MajenkoProjects/TerminalServer/TerminalServer/Firmware/src/config/default/driver/spi/src/drv_spi.c

/*******************************************************************************
  SPI Driver Implementation.

  Company:
    Microchip Technology Inc.

  File Name:
    drv_spi.c

  Summary:
    Source code for the SPI driver implementation.

  Description:
    This file contains the source code for the implementation of the SPI driver.
*******************************************************************************/

//DOM-IGNORE-BEGIN
/*******************************************************************************
* Copyright (C) 2018 Microchip Technology Inc. and its subsidiaries.
*
* Subject to your compliance with these terms, you may use Microchip software
* and any derivatives exclusively with Microchip products. It is your
* responsibility to comply with third party license terms applicable to your
* use of third party software (including open source software) that may
* accompany Microchip software.
*
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
* IN NO EVENT WILL MICROCHIP BE LIABLE FOR ANY INDIRECT, SPECIAL, PUNITIVE,
* INCIDENTAL OR CONSEQUENTIAL LOSS, DAMAGE, COST OR EXPENSE OF ANY KIND
* WHATSOEVER RELATED TO THE SOFTWARE, HOWEVER CAUSED, EVEN IF MICROCHIP HAS
* BEEN ADVISED OF THE POSSIBILITY OR THE DAMAGES ARE FORESEEABLE. TO THE
* FULLEST EXTENT ALLOWED BY LAW, MICROCHIP'S TOTAL LIABILITY ON ALL CLAIMS IN
* ANY WAY RELATED TO THIS SOFTWARE WILL NOT EXCEED THE AMOUNT OF FEES, IF ANY,
* THAT YOU HAVE PAID DIRECTLY TO MICROCHIP FOR THIS SOFTWARE.
*******************************************************************************/
//DOM-IGNORE-END

// *****************************************************************************
// *****************************************************************************
// Section: Included Files
// *****************************************************************************
// *****************************************************************************

#include <string.h>
#include "configuration.h"
#include "driver/spi/drv_spi.h"
#include "system/debug/sys_debug.h"

// *****************************************************************************
// *****************************************************************************
// Section: Global Data
// *****************************************************************************
// *****************************************************************************

/* This is the driver instance object array. */
static CACHE_ALIGN DRV_SPI_OBJ gDrvSPIObj[DRV_SPI_INSTANCES_NUMBER];

// *****************************************************************************
// *****************************************************************************
// Section: File scope functions
// *****************************************************************************
// *****************************************************************************

static void lDRV_SPI_TX_DMA_CallbackHandler(SYS_DMA_TRANSFER_EVENT event, uintptr_t context);
static void lDRV_SPI_RX_DMA_CallbackHandler(SYS_DMA_TRANSFER_EVENT event, uintptr_t context);

static inline uint32_t  lDRV_SPI_MAKE_HANDLE(uint16_t token, uint8_t drvIndex, uint8_t index)
{
    return (((uint32_t)token << 16) | ((uint32_t)drvIndex << 8) | index);
}

static inline uint16_t lDRV_SPI_UPDATE_TOKEN(uint16_t token)
{
    token++;

    if (token >= DRV_SPI_TOKEN_MAX)
    {
        token = 1;
    }

    return token;
}

static void lDRV_SPI_DisableInterrupts(DRV_SPI_OBJ* dObj)
{
    bool interruptStatus;
    const DRV_SPI_INTERRUPT_SOURCES* intInfo = dObj->interruptSources;
    const DRV_SPI_MULTI_INT_SRC* multiVector = &intInfo->intSources.multi;
    /* Disable DMA interrupt */
    if((dObj->txDMAChannel != SYS_DMA_CHANNEL_NONE) && (dObj->rxDMAChannel != SYS_DMA_CHANNEL_NONE))
    {
        if (intInfo->isSingleIntSrc == true)
        {
            dObj->dmaInterruptStatus = SYS_INT_SourceDisable((INT_SOURCE)intInfo->intSources.dmaInterrupt);
        }
        else
        {
            /* Disable DMA interrupt sources */
            interruptStatus = SYS_INT_Disable();

            dObj->dmaTxChannelIntStatus = SYS_INT_SourceDisable((INT_SOURCE)multiVector->dmaTxChannelInt);
            dObj->dmaRxChannelIntStatus = SYS_INT_SourceDisable((INT_SOURCE)multiVector->dmaRxChannelInt);

            SYS_INT_Restore(interruptStatus);
        }
    }
    else
    {
        /* Disable SPI interrupt */
        if (intInfo->isSingleIntSrc == true)
        {
            dObj->spiInterruptStatus = SYS_INT_SourceDisable((INT_SOURCE)intInfo->intSources.spiInterrupt);
        }
        else
        {
            interruptStatus = SYS_INT_Disable();
            if(multiVector->spiTxReadyInt != -1)
            {
                dObj->spiTxReadyIntStatus = SYS_INT_SourceDisable((INT_SOURCE)multiVector->spiTxReadyInt);
            }
            if(multiVector->spiTxCompleteInt != -1)
            {
                dObj->spiTxCompleteIntStatus = SYS_INT_SourceDisable((INT_SOURCE)multiVector->spiTxCompleteInt);
            }
            if(multiVector->spiRxInt != -1)
            {
                dObj->spiRxIntStatus = SYS_INT_SourceDisable((INT_SOURCE)multiVector->spiRxInt);
            }
            SYS_INT_Restore(interruptStatus);
        }
    }
}

static void lDRV_SPI_EnableInterrupts(DRV_SPI_OBJ* dObj)
{
    bool interruptStatus;
    const DRV_SPI_INTERRUPT_SOURCES* intInfo = dObj->interruptSources;
    const DRV_SPI_MULTI_INT_SRC* multiVector = &intInfo->intSources.multi;
    /* Enable DMA interrupt */
    if((dObj->txDMAChannel != SYS_DMA_CHANNEL_NONE) && (dObj->rxDMAChannel != SYS_DMA_CHANNEL_NONE))
    {
        if (intInfo->isSingleIntSrc == true)
        {
            SYS_INT_SourceRestore((INT_SOURCE)intInfo->intSources.dmaInterrupt, dObj->dmaInterruptStatus);
        }
        else
        {
            interruptStatus = SYS_INT_Disable();

            /* Enable DMA interrupt sources */
            SYS_INT_SourceRestore((INT_SOURCE)multiVector->dmaTxChannelInt, dObj->dmaTxChannelIntStatus);
            SYS_INT_SourceRestore((INT_SOURCE)multiVector->dmaRxChannelInt, dObj->dmaRxChannelIntStatus);

            SYS_INT_Restore(interruptStatus);
        }
    }
    else
    {
        /* Enable SPI interrupt */
        if (intInfo->isSingleIntSrc == true)
        {
            SYS_INT_SourceRestore((INT_SOURCE)intInfo->intSources.spiInterrupt, dObj->spiInterruptStatus);
        }
        else
        {
            interruptStatus = SYS_INT_Disable();
            if(multiVector->spiTxReadyInt != -1)
            {
                SYS_INT_SourceRestore((INT_SOURCE)multiVector->spiTxReadyInt, dObj->spiTxReadyIntStatus);
            }
            if(multiVector->spiTxCompleteInt != -1)
            {
                SYS_INT_SourceRestore((INT_SOURCE)multiVector->spiTxCompleteInt,dObj->spiTxCompleteIntStatus);
            }
            if(multiVector->spiRxInt != -1)
            {
                SYS_INT_SourceRestore((INT_SOURCE)multiVector->spiRxInt, dObj->spiRxIntStatus);
            }
            SYS_INT_Restore(interruptStatus);
        }
    }
}


static bool lDRV_SPI_ResourceLock(DRV_SPI_OBJ * dObj)
{
    /* We will allow buffers to be added in the interrupt context of the SPI
     * driver. But we must make sure that if we are inside interrupt, then we
     * should not modify mutexes. */
    if(dObj->interruptNestingCount == 0U)
    {
        /* Grab a mutex. This is okay because we are not in an interrupt context */
        if(OSAL_MUTEX_Lock(&(dObj->mutexTransferObjects), OSAL_WAIT_FOREVER) == OSAL_RESULT_FAIL)
        {
            return false;
        }
        /* We will disable interrupts so that the queue status does not get updated asynchronously */
        lDRV_SPI_DisableInterrupts(dObj);
    }

    return true;
}

static void lDRV_SPI_ResourceUnlock(DRV_SPI_OBJ * dObj)
{
    if(dObj->interruptNestingCount == 0U)
    {
        lDRV_SPI_EnableInterrupts(dObj);

        /* Release mutex */
        (void) OSAL_MUTEX_Unlock(&(dObj->mutexTransferObjects));
    }
}

static DRV_SPI_CLIENT_OBJ * lDRV_SPI_DriverHandleValidate(DRV_HANDLE handle)
{
    /* This function returns the pointer to the client object that is
       associated with this handle if the handle is valid. Returns NULL
       otherwise. */

    uint32_t drvInstance = 0;
    DRV_SPI_CLIENT_OBJ* clientObj = (DRV_SPI_CLIENT_OBJ*)NULL;

    if((handle != DRV_HANDLE_INVALID) && (handle != 0U))
    {
        /* Extract the drvInstance value from the handle */
        drvInstance = ((handle & DRV_SPI_INSTANCE_MASK) >> 8);

        if (drvInstance >= DRV_SPI_INSTANCES_NUMBER)
        {
            return (NULL);
        }

        if ((handle & DRV_SPI_INDEX_MASK) >= gDrvSPIObj[drvInstance].nClientsMax)
        {
            return (NULL);
        }

        /* Extract the client index and obtain the client object */
        clientObj = &((DRV_SPI_CLIENT_OBJ *)gDrvSPIObj[drvInstance].clientObjPool)[handle & DRV_SPI_INDEX_MASK];

        if ((clientObj->clientHandle != handle) || (clientObj->inUse == false))
        {
            return (NULL);
        }
    }

    return(clientObj);
}

static DRV_SPI_TRANSFER_OBJ* lDRV_SPI_FreeTransferObjGet(DRV_SPI_CLIENT_OBJ* clientObj)
{
    uint32_t i;
    uint32_t index;
    DRV_SPI_OBJ* dObj = (DRV_SPI_OBJ* )&gDrvSPIObj[clientObj->drvIndex];
    DRV_SPI_TRANSFER_OBJ* pTransferObj = (DRV_SPI_TRANSFER_OBJ*)dObj->transferObjPool;

    i = 0;
    index = dObj->transferObjLastUsedIndex;
    while(i < dObj->transferObjPoolSize)
    {
        if (index >= dObj->transferObjPoolSize)
        {
            index = 0;
        }
        if (pTransferObj[index].inUse == false)
        {
            pTransferObj[index].inUse = true;
            pTransferObj[index].next = NULL;

            /* Generate a unique buffer handle consisting of an incrementing
             * token counter, driver index and the buffer index.
             */
            pTransferObj[index].transferHandle = (DRV_SPI_TRANSFER_HANDLE)lDRV_SPI_MAKE_HANDLE(
                dObj->spiTokenCount, (uint8_t)clientObj->drvIndex, (uint8_t)index);

            /* Update the token for next time */
            dObj->spiTokenCount = lDRV_SPI_UPDATE_TOKEN(dObj->spiTokenCount);

            dObj->transferObjLastUsedIndex = index + 1U;

            return &pTransferObj[index];
        }
        i++;
        index++;
    }
    return NULL;
}
/* MISRA C-2023 Rule 11.3, 11.8 deviated below. Deviation record ID -
   H3_MISRAC_2023_R_11_3_DR_1 & H3_MISRAC_2023_R_11_8_DR_1*/

static bool lDRV_SPI_TransferObjAddToList(
    DRV_SPI_OBJ* dObj,
    DRV_SPI_TRANSFER_OBJ* transferObj
)
{
    DRV_SPI_TRANSFER_OBJ** pTransferObjList;
    bool isFirstTransferInList = false;

    pTransferObjList = (DRV_SPI_TRANSFER_OBJ**)&(dObj->transferObjList);

    // Is the buffer object list empty?
    if (*pTransferObjList == NULL)
    {
        *pTransferObjList = transferObj;
        isFirstTransferInList = true;
    }
    else
    {
        // List is not empty. Iterate to the end of the buffer object list.
        while (*pTransferObjList != NULL)
        {
            if ((*pTransferObjList)->next == NULL)
            {
                // End of the list reached, add the buffer here.
                (*pTransferObjList)->next = transferObj;
                break;
            }
            else
            {
                pTransferObjList = (DRV_SPI_TRANSFER_OBJ**)&((*pTransferObjList)->next);
            }
        }
    }

    return isFirstTransferInList;
}

static DRV_SPI_TRANSFER_OBJ* lDRV_SPI_TransferObjListGet( DRV_SPI_OBJ* dObj )
{
    DRV_SPI_TRANSFER_OBJ* pTransferObj = NULL;

    // Return the element at the head of the linked list
    pTransferObj = (DRV_SPI_TRANSFER_OBJ*)dObj->transferObjList;

    return pTransferObj;
}

static void lDRV_SPI_RemoveTransferObjFromList( DRV_SPI_OBJ* dObj )
{
    DRV_SPI_TRANSFER_OBJ** pTransferObjList;

    pTransferObjList = (DRV_SPI_TRANSFER_OBJ**)&(dObj->transferObjList);

    // Remove the element at the head of the linked list
    if (*pTransferObjList != NULL)
    {
        /* Save the buffer object to be removed. Set the next buffer object as
         * the new head of the linked list. Reset the removed buffer object. */

        DRV_SPI_TRANSFER_OBJ* temp = *pTransferObjList;
        *pTransferObjList = (*pTransferObjList)->next;
        temp->currentState = DRV_SPI_TRANSFER_OBJ_IS_FREE;
        temp->next = NULL;
        temp->inUse = false;
    }
}

static void lDRV_SPI_RemoveClientTransfersFromList(
    DRV_SPI_OBJ* dObj,
    DRV_SPI_CLIENT_OBJ* clientObj
)
{
    DRV_SPI_TRANSFER_OBJ** pTransferObjList;
    DRV_SPI_TRANSFER_OBJ* delTransferObj = NULL;

    pTransferObjList = (DRV_SPI_TRANSFER_OBJ**)&(dObj->transferObjList);

    while (*pTransferObjList != NULL)
    {
        // Do not remove the buffer object that is already in process
        if (((*pTransferObjList)->clientHandle == clientObj->clientHandle) &&
                ((*pTransferObjList)->currentState == DRV_SPI_TRANSFER_OBJ_IS_IN_QUEUE))
        {
            // Save the node to be deleted off the list
            delTransferObj = *pTransferObjList;

            // Update the current node to point to the deleted node's next
            *pTransferObjList = (DRV_SPI_TRANSFER_OBJ*)(*pTransferObjList)->next;

            // Reset the deleted node
            delTransferObj->currentState = DRV_SPI_TRANSFER_OBJ_IS_FREE;
            delTransferObj->event = DRV_SPI_TRANSFER_EVENT_COMPLETE;
            delTransferObj->next = NULL;
            delTransferObj->inUse = false;
        }
        else
        {
            // Move to the next node
            pTransferObjList = (DRV_SPI_TRANSFER_OBJ**)&((*pTransferObjList)->next);
        }
    }
}

/* MISRA C-2023 Rule 11.1 deviated:2 Deviation record ID -  H3_MISRAC_2023_R_11_1_DR_1 */

static void lDRV_SPI_StartDMATransfer(DRV_SPI_TRANSFER_OBJ* transferObj)
{
    DRV_SPI_CLIENT_OBJ* clientObj;
    DRV_SPI_OBJ* dObj;
    uint32_t size = 0;
    /* To avoid unused build error */
    (void) size;

    /* Get the client object that owns this buffer */
    clientObj = &((DRV_SPI_CLIENT_OBJ *)gDrvSPIObj[((transferObj->clientHandle & DRV_SPI_INSTANCE_MASK) >> 8)].clientObjPool)
    [transferObj->clientHandle & DRV_SPI_INDEX_MASK];

    dObj = (DRV_SPI_OBJ*)&gDrvSPIObj[clientObj->drvIndex];

    /* Initialize the dummy data buffer with 0xFF */
    (void)memset(dObj->dummyDataBuffer, 0xFF, sizeof(dObj->dummyDataBuffer));

    transferObj->nBytesTransferred = 0;

    transferObj->txPending = transferObj->txSize;
    transferObj->rxPending = transferObj->rxSize;

    /* Register callbacks for DMA */
    SYS_DMA_ChannelCallbackRegister(dObj->txDMAChannel, lDRV_SPI_TX_DMA_CallbackHandler, (uintptr_t)transferObj);
    SYS_DMA_ChannelCallbackRegister(dObj->rxDMAChannel, lDRV_SPI_RX_DMA_CallbackHandler, (uintptr_t)transferObj);

    SYS_DMA_AddressingModeSetup(dObj->rxDMAChannel, SYS_DMA_SOURCE_ADDRESSING_MODE_FIXED, SYS_DMA_DESTINATION_ADDRESSING_MODE_INCREMENTED);
    SYS_DMA_AddressingModeSetup(dObj->txDMAChannel, SYS_DMA_SOURCE_ADDRESSING_MODE_INCREMENTED, SYS_DMA_DESTINATION_ADDRESSING_MODE_FIXED);

    if(clientObj->setup.dataBits == DRV_SPI_DATA_BITS_8)
    {
        SYS_DMA_DataWidthSetup(dObj->rxDMAChannel, SYS_DMA_WIDTH_8_BIT);
        SYS_DMA_DataWidthSetup(dObj->txDMAChannel, SYS_DMA_WIDTH_8_BIT);
    }
    else if (clientObj->setup.dataBits <= DRV_SPI_DATA_BITS_16)
    {
        SYS_DMA_DataWidthSetup(dObj->rxDMAChannel, SYS_DMA_WIDTH_16_BIT);
        SYS_DMA_DataWidthSetup(dObj->txDMAChannel, SYS_DMA_WIDTH_16_BIT);
    }
    else
    {
        SYS_DMA_DataWidthSetup(dObj->rxDMAChannel, SYS_DMA_WIDTH_32_BIT);
        SYS_DMA_DataWidthSetup(dObj->txDMAChannel, SYS_DMA_WIDTH_32_BIT);
    }

    if ((transferObj->txPending > 0U) && (transferObj->rxPending > 0U))
    {
        /* Find the lower value among rxPending and txPending*/

        (transferObj->txPending >= transferObj->rxPending) ?
            (size = transferObj->rxPending) : (size = transferObj->txPending);

        /* Calculate the remaining tx/rx bytes and total bytes transferred */
        transferObj->rxPending -= size;
        transferObj->txPending -= size;
        transferObj->nBytesTransferred += size;

        /* Always set up the rx channel first */
        (void) SYS_DMA_ChannelTransfer(dObj->rxDMAChannel, dObj->rxAddress, transferObj->pReceiveData, size);
        (void) SYS_DMA_ChannelTransfer(dObj->txDMAChannel, transferObj->pTransmitData, dObj->txAddress, size);
    }
    else
    {
        if (transferObj->rxPending > 0U)
        {
            /* txPending is 0. Need to use the dummy data buffer for transmission.
             * Find out the max data that can be received, given the limited size of the dummy data buffer.
             */
            (transferObj->rxPending > sizeof(dObj->dummyDataBuffer)) ?
                (size = sizeof(dObj->dummyDataBuffer)): (size = transferObj->rxPending);

            /* Calculate the remaining rx bytes and total bytes transferred */
            transferObj->rxPending -= size;
            transferObj->nBytesTransferred += size;

            /* Always set up the rx channel first */
            (void) SYS_DMA_ChannelTransfer(dObj->rxDMAChannel, dObj->rxAddress, transferObj->pReceiveData, size);
            (void) SYS_DMA_ChannelTransfer(dObj->txDMAChannel, dObj->dummyDataBuffer, dObj->txAddress, size);

        }
        else
        {
            /* rxPending is 0. Need to use the dummy data buffer for reception.
             * Find out the max data that can be transmitted, given the limited size of the dummy data buffer.
             */
            (transferObj->txPending > sizeof(dObj->dummyDataBuffer)) ?
                (size = sizeof(dObj->dummyDataBuffer)): (size = transferObj->txPending);

            /* Calculate the remaining tx bytes and total bytes transferred */
            transferObj->txPending -= size;
            transferObj->nBytesTransferred += size;

            /* Always set up the rx channel first */
            (void) SYS_DMA_ChannelTransfer(dObj->rxDMAChannel, dObj->rxAddress, dObj->dummyDataBuffer, size);
            (void) SYS_DMA_ChannelTransfer(dObj->txDMAChannel, transferObj->pTransmitData, dObj->txAddress, size);
        }
    }
}
/* MISRAC 2012 deviation block end */

static void lDRV_SPI_UpdateTransferSetupAndAssertCS(
    DRV_SPI_TRANSFER_OBJ* transferObj
)
{
    DRV_SPI_OBJ* dObj;
    DRV_SPI_CLIENT_OBJ* clientObj;
    DRV_SPI_TRANSFER_SETUP setupRemap;

    /* Get the client object that owns this buffer */
    clientObj = &((DRV_SPI_CLIENT_OBJ *)gDrvSPIObj[((transferObj->clientHandle & DRV_SPI_INSTANCE_MASK) >> 8)].clientObjPool)
    [transferObj->clientHandle & DRV_SPI_INDEX_MASK];

    dObj = (DRV_SPI_OBJ*)&gDrvSPIObj[clientObj->drvIndex];

    /* Update the PLIB Setup if current request is from a different client or
     * setup has been changed dynamically for the client */
    if((transferObj->clientHandle != dObj->lastClientHandle) || (clientObj->setupChanged == true))
    {
        setupRemap = clientObj->setup;
        setupRemap.clockPolarity = (DRV_SPI_CLOCK_POLARITY)dObj->remapClockPolarity[clientObj->setup.clockPolarity];
        setupRemap.clockPhase = (DRV_SPI_CLOCK_PHASE)dObj->remapClockPhase[clientObj->setup.clockPhase];
        setupRemap.dataBits = (DRV_SPI_DATA_BITS)dObj->remapDataBits[clientObj->setup.dataBits];

        (void) dObj->spiPlib->setup(&setupRemap, USE_FREQ_CONFIGURED_IN_CLOCK_MANAGER);
        dObj->lastClientHandle = transferObj->clientHandle;
        clientObj->setupChanged = false;
    }

    /* Assert chip select if configured */
    if(clientObj->setup.chipSelect != SYS_PORT_PIN_NONE)
    {
        if (clientObj->setup.csPolarity == DRV_SPI_CS_POLARITY_ACTIVE_LOW)
        {
            SYS_PORT_PinClear(clientObj->setup.chipSelect);
        }
        else
        {
            SYS_PORT_PinSet(clientObj->setup.chipSelect);
        }
    }
}

static void lDRV_SPI_PlibCallbackHandler(uintptr_t contextHandle)
{
    DRV_SPI_OBJ* dObj                    = (DRV_SPI_OBJ*)contextHandle;
    DRV_SPI_CLIENT_OBJ* clientObj        = (DRV_SPI_CLIENT_OBJ*)NULL;
    DRV_SPI_TRANSFER_OBJ* transferObj    = (DRV_SPI_TRANSFER_OBJ*)NULL;
    DRV_SPI_TRANSFER_EVENT event;
    DRV_SPI_TRANSFER_HANDLE transferHandle;

    if((dObj->inUse == false) || (dObj->status != SYS_STATUS_READY))
    {
        /* This instance of the driver is not initialized. Don't
         * do anything */
        return;
    }

    /* Get the transfer object at the head of the list */
    transferObj = lDRV_SPI_TransferObjListGet(dObj);

    /* Get the client object that owns this buffer */
    clientObj = &((DRV_SPI_CLIENT_OBJ *)gDrvSPIObj[((transferObj->clientHandle & DRV_SPI_INSTANCE_MASK) >> 8)].clientObjPool)
    [transferObj->clientHandle & DRV_SPI_INDEX_MASK];

    /* De-assert Chip Select if it is defined by user */
    if(clientObj->setup.chipSelect != SYS_PORT_PIN_NONE)
    {
        if (clientObj->setup.csPolarity == DRV_SPI_CS_POLARITY_ACTIVE_LOW)
        {
            SYS_PORT_PinSet(clientObj->setup.chipSelect);
        }
        else
        {
            SYS_PORT_PinClear(clientObj->setup.chipSelect);
        }
    }

    /* Check if the client that submitted the request is active? */
    if (clientObj->clientHandle == transferObj->clientHandle)
    {
        transferObj->event = DRV_SPI_TRANSFER_EVENT_COMPLETE;

        /* Save the transfer handle and event locally before freeing the transfer object*/
        event = transferObj->event;
        transferHandle = transferObj->transferHandle;

        /* Free the completed buffer.
         * This is done before giving callback to allow application to use the freed
         * buffer and queue in a new request from within the callback */

        lDRV_SPI_RemoveTransferObjFromList(dObj);

        if(clientObj->eventHandler != NULL)
        {
            /* Call the event handler. We additionally increment the
            interrupt nesting count which lets the driver functions
            that are called from the event handler know that an
            interrupt context is active. */
            dObj->interruptNestingCount++;

            clientObj->eventHandler(event, transferHandle, clientObj->context);

            /* Event handler has completed, so decrement the nesting count now */
            dObj->interruptNestingCount--;
        }
    }
    else
    {
        /* Free the completed buffer */
        lDRV_SPI_RemoveTransferObjFromList(dObj);
    }

     /* Get the transfer object at the head of the list */
    transferObj = lDRV_SPI_TransferObjListGet(dObj);

    /* Process the next transfer buffer */
    if((transferObj != NULL) && (transferObj->currentState == DRV_SPI_TRANSFER_OBJ_IS_IN_QUEUE))
    {
        lDRV_SPI_UpdateTransferSetupAndAssertCS(transferObj);

        transferObj->currentState = DRV_SPI_TRANSFER_OBJ_IS_PROCESSING;

        (void) dObj->spiPlib->writeRead(
            transferObj->pTransmitData,
            transferObj->txSize,
            transferObj->pReceiveData,
            transferObj->rxSize
        );
    }
}

/* Locks the SPI driver for exclusive use by a client */
static bool DRV_SPI_ExclusiveUse( const DRV_HANDLE handle, bool useExclusive )
{
    DRV_SPI_CLIENT_OBJ* clientObj = NULL;
    DRV_SPI_OBJ* dObj = (DRV_SPI_OBJ*)NULL;
    bool isSuccess = false;

    /* Validate the driver handle */
    clientObj = lDRV_SPI_DriverHandleValidate(handle);

    if (clientObj != NULL)
    {
        dObj = (DRV_SPI_OBJ *)&gDrvSPIObj[clientObj->drvIndex];

        if (useExclusive == true)
        {
            if (dObj->drvInExclusiveMode == true)
            {
                if (dObj->exclusiveUseClientHandle == handle)
                {
                    dObj->exclusiveUseCntr++;
                    isSuccess = true;
                }
            }
            else
            {
                /* Guard against multiple threads trying to lock the driver */
                if (OSAL_MUTEX_Lock(&dObj->mutexExclusiveUse , OSAL_WAIT_FOREVER ) == OSAL_RESULT_FAIL)
                {
                    isSuccess = false;
                }
                else
                {
                    dObj->drvInExclusiveMode = true;
                    dObj->exclusiveUseClientHandle = handle;
                    dObj->exclusiveUseCntr++;
                    isSuccess = true;
                }
            }
        }
        else
        {
            if (dObj->exclusiveUseClientHandle == handle)
            {
                if (dObj->exclusiveUseCntr > 0U)
                {
                    dObj->exclusiveUseCntr--;
                    if (dObj->exclusiveUseCntr == 0U)
                    {
                        dObj->exclusiveUseClientHandle = DRV_HANDLE_INVALID;
                        dObj->drvInExclusiveMode = false;

                        (void) OSAL_MUTEX_Unlock( &dObj->mutexExclusiveUse);
                    }
                }
                isSuccess = true;
            }
        }
    }

    return isSuccess;
}

static void lDRV_SPI_TX_DMA_CallbackHandler(
    SYS_DMA_TRANSFER_EVENT event,
    uintptr_t context
)
{
    (void)event;
    (void)context;
}

static void lDRV_SPI_RX_DMA_CallbackHandler(
    SYS_DMA_TRANSFER_EVENT event,
    uintptr_t context
)
{
    DRV_SPI_TRANSFER_OBJ* transferObj = (DRV_SPI_TRANSFER_OBJ*)context;
    DRV_SPI_CLIENT_OBJ* clientObj;
    DRV_SPI_OBJ* dObj;
    DRV_SPI_TRANSFER_EVENT transferEvent;
    DRV_SPI_TRANSFER_HANDLE transferHandle;
    uint32_t size;
    uint32_t index;

    /* Get the client object that owns this buffer */
    clientObj = &((DRV_SPI_CLIENT_OBJ *)gDrvSPIObj[((transferObj->clientHandle & DRV_SPI_INSTANCE_MASK) >> 8)].clientObjPool)
    [transferObj->clientHandle & DRV_SPI_INDEX_MASK];

    dObj = &gDrvSPIObj[clientObj->drvIndex];

    if (transferObj->rxPending > 0U)
    {
        /* txPending is 0. Need to use the dummy data buffer for transmission.
         * Find out the max data that can be received, given the limited size of the dummy data buffer.
         */
        (transferObj->rxPending > sizeof(dObj->dummyDataBuffer)) ?
            (size = sizeof(dObj->dummyDataBuffer)): (size = transferObj->rxPending);

        index = transferObj->nBytesTransferred;

        /* Calculate the remaining rx bytes and total bytes transferred */
        transferObj->rxPending -= size;
        transferObj->nBytesTransferred += size;

        /* Always set up the rx channel first */
        (void) SYS_DMA_ChannelTransfer(dObj->rxDMAChannel, dObj->rxAddress, &((uint8_t*)transferObj->pReceiveData)[index], size);
        (void) SYS_DMA_ChannelTransfer(dObj->txDMAChannel, dObj->dummyDataBuffer, dObj->txAddress, size);

    }
    else if (transferObj->txPending > 0U)
    {
        /* rxPending is 0. Need to use the dummy data buffer for reception.
         * Find out the max data that can be transmitted, given the limited size of the dummy data buffer.
         */
        (transferObj->txPending > sizeof(dObj->dummyDataBuffer)) ?
            (size = sizeof(dObj->dummyDataBuffer)): (size = transferObj->txPending);

        index = transferObj->nBytesTransferred;

        /* Calculate the remaining tx bytes and total bytes transferred */
        transferObj->txPending -= size;
        transferObj->nBytesTransferred += size;

        /* Always set up the rx channel first */
        (void) SYS_DMA_ChannelTransfer(dObj->rxDMAChannel, dObj->rxAddress, dObj->dummyDataBuffer, size);
        (void) SYS_DMA_ChannelTransfer(dObj->txDMAChannel, &((uint8_t*)transferObj->pTransmitData)[index], dObj->txAddress, size);
    }
    else
    {
        /* Make sure the shift register is empty before de-asserting the CS line */
        while (dObj->spiPlib->isTransmitterBusy())
        {
            /* Do Nothing */
        }

        /* Transfer complete. De-assert Chip Select if it is defined by user. */
        if(clientObj->setup.chipSelect != SYS_PORT_PIN_NONE)
        {
            if (clientObj->setup.csPolarity == DRV_SPI_CS_POLARITY_ACTIVE_LOW)
            {
                SYS_PORT_PinSet(clientObj->setup.chipSelect);
            }
            else
            {
                SYS_PORT_PinClear(clientObj->setup.chipSelect);
            }
        }

        /* Check if the client that submitted the request is active? */
        if (clientObj->clientHandle == transferObj->clientHandle)
        {
            /* Set the events */
            if(event == SYS_DMA_TRANSFER_COMPLETE)
            {
                transferObj->event = DRV_SPI_TRANSFER_EVENT_COMPLETE;
            }
            else if(event == SYS_DMA_TRANSFER_ERROR)
            {
                transferObj->event = DRV_SPI_TRANSFER_EVENT_ERROR;
            }
            else
            {
                /* Do Nothing */
            }

            /* Save the transfer handle and event locally before freeing the transfer object*/
            transferEvent = transferObj->event;
            transferHandle = transferObj->transferHandle;

            /* Free the completed buffer.
             * This is done before giving callback to allow application to use the freed
             * buffer and queue in a new request from within the callback */

            lDRV_SPI_RemoveTransferObjFromList(dObj);

            if(clientObj->eventHandler != NULL)
            {
                /* Call the event handler. We additionally increment the
                interrupt nesting count which lets the driver functions
                that are called from the event handler know that an
                interrupt context is active. */
                dObj->interruptNestingCount++;

                clientObj->eventHandler(transferEvent, transferHandle, clientObj->context);

                /* Event handler has completed, so decrement the nesting count now */
                dObj->interruptNestingCount--;
            }
        }
        else
        {
            /* Free the completed buffer */
            lDRV_SPI_RemoveTransferObjFromList(dObj);
        }

        /* Get the next transfer object at the head of the list */
        transferObj = lDRV_SPI_TransferObjListGet(dObj);

        if((transferObj != NULL) && (transferObj->currentState == DRV_SPI_TRANSFER_OBJ_IS_IN_QUEUE))
        {
            /* Process the next transfer buffer */
            lDRV_SPI_UpdateTransferSetupAndAssertCS(transferObj);
            transferObj->currentState = DRV_SPI_TRANSFER_OBJ_IS_PROCESSING;
            lDRV_SPI_StartDMATransfer(transferObj);
        }
    }
}


// *****************************************************************************
// *****************************************************************************
// Section: SPI Driver Common Interface Implementation
// *****************************************************************************
// *****************************************************************************

SYS_MODULE_OBJ DRV_SPI_Initialize (
    const SYS_MODULE_INDEX drvIndex,
    const SYS_MODULE_INIT* const init
)
{
    DRV_SPI_OBJ* dObj = (DRV_SPI_OBJ*)NULL;
    DRV_SPI_INIT* spiInit = (DRV_SPI_INIT*)init;


    /* Validate the request */
    if(drvIndex >= DRV_SPI_INSTANCES_NUMBER)
    {
        SYS_DEBUG_MESSAGE(SYS_ERROR_ERROR, "Invalid driver instance");
        return SYS_MODULE_OBJ_INVALID;
    }

    if(gDrvSPIObj[drvIndex].inUse == true)
    {
        SYS_DEBUG_MESSAGE(SYS_ERROR_ERROR, "Instance already in use");
        return SYS_MODULE_OBJ_INVALID;
    }

    /* Allocate the driver object */
    dObj = &gDrvSPIObj[drvIndex];

    /* Create mutexes */
    if(OSAL_MUTEX_Create(&(dObj->mutexClientObjects)) != OSAL_RESULT_SUCCESS)
    {
        return SYS_MODULE_OBJ_INVALID;
    }

    if(OSAL_MUTEX_Create(&(dObj->mutexTransferObjects)) != OSAL_RESULT_SUCCESS)
    {
        return SYS_MODULE_OBJ_INVALID;
    }

    if(OSAL_MUTEX_Create(&(dObj->mutexExclusiveUse)) != OSAL_RESULT_SUCCESS)
    {
        return SYS_MODULE_OBJ_INVALID;
    }

    dObj->inUse = true;

    /* Update the driver parameters */
    dObj->spiPlib                   = spiInit->spiPlib;
    dObj->transferObjPool           = (DRV_SPI_TRANSFER_OBJ*)spiInit->transferObjPool;
    dObj->transferObjPoolSize       = spiInit->transferObjPoolSize;
    dObj->transferObjList           = 0U;
    dObj->clientObjPool             = spiInit->clientObjPool;
    dObj->nClientsMax               = spiInit->numClients;
    dObj->nClients                  = 0;
    dObj->spiTokenCount             = 1;
    dObj->lastClientHandle          = DRV_HANDLE_INVALID;
    dObj->interruptNestingCount     = 0;
    dObj->isExclusive               = false;
    dObj->txDMAChannel              = spiInit->dmaChannelTransmit;
    dObj->rxDMAChannel              = spiInit->dmaChannelReceive;
    dObj->txAddress                 = spiInit->spiTransmitAddress;
    dObj->rxAddress                 = spiInit->spiReceiveAddress;
    dObj->remapDataBits             = spiInit->remapDataBits;
    dObj->remapClockPolarity        = spiInit->remapClockPolarity;
    dObj->remapClockPhase           = spiInit->remapClockPhase;
    dObj->interruptSources          = spiInit->interruptSources;
    dObj->drvInExclusiveMode        = false;
    dObj->exclusiveUseCntr          = 0;
    dObj->transferObjLastUsedIndex  = 0;


    if((dObj->txDMAChannel == SYS_DMA_CHANNEL_NONE) || (dObj->rxDMAChannel == SYS_DMA_CHANNEL_NONE))
    {
        /* Register a callback with SPI PLIB.
         * dObj as a context parameter will be used to distinguish the events
         * from different instances. */
        dObj->spiPlib->callbackRegister(&lDRV_SPI_PlibCallbackHandler, (uintptr_t)dObj);
    }
    else
    {
        /* This means DMA has to be used for SPI transfer.
         * DMA Callbacks will be set for every transfer later. */
    }

    /* Update the status */
    dObj->status = SYS_STATUS_READY;

    /* Return the object structure */
    return ( (SYS_MODULE_OBJ)drvIndex );
}
/* MISRAC 2012 deviation block end */

SYS_STATUS DRV_SPI_Status( SYS_MODULE_OBJ object)
{
    /* Validate the request */
    if((object == SYS_MODULE_OBJ_INVALID) || (object >= DRV_SPI_INSTANCES_NUMBER))
    {
        SYS_DEBUG_MESSAGE(SYS_ERROR_ERROR, "Invalid system object handle");
        return SYS_STATUS_UNINITIALIZED;
    }

    return (gDrvSPIObj[object].status);
}

DRV_HANDLE DRV_SPI_Open(
    const SYS_MODULE_INDEX drvIndex,
    const DRV_IO_INTENT ioIntent
)
{
    DRV_SPI_CLIENT_OBJ* clientObj;
    DRV_SPI_OBJ* dObj = NULL;
    uint32_t iClient;
    uint32_t temp;

    /* Validate the request */
    if (drvIndex >= DRV_SPI_INSTANCES_NUMBER)
    {
        SYS_DEBUG_MESSAGE(SYS_ERROR_ERROR, "Invalid Driver Instance");
        return DRV_HANDLE_INVALID;
    }

    dObj = &gDrvSPIObj[drvIndex];

    /* Guard against multiple threads trying to open the driver */
    if (OSAL_MUTEX_Lock(&dObj->mutexClientObjects , OSAL_WAIT_FOREVER ) == OSAL_RESULT_FAIL)
    {
        return DRV_HANDLE_INVALID;
    }

    if((dObj->status != SYS_STATUS_READY) || (dObj->inUse == false))
    {
        SYS_DEBUG_MESSAGE(SYS_ERROR_ERROR, "Was the driver initialized?");
        (void) OSAL_MUTEX_Unlock( &dObj->mutexClientObjects);
        return DRV_HANDLE_INVALID;
    }

    if(dObj->isExclusive == true)
    {
        /* Driver is already opened with exclusive access. Hence, cannot be opened again*/
        (void) OSAL_MUTEX_Unlock( &dObj->mutexClientObjects);
        return DRV_HANDLE_INVALID;
    }

    if((dObj->nClients > 0U) && (((uint32_t)ioIntent & (uint32_t)DRV_IO_INTENT_EXCLUSIVE) != 0U))
    {
        /* Exclusive access is requested while the driver is already opened by other client */
        (void) OSAL_MUTEX_Unlock( &dObj->mutexClientObjects);
        return(DRV_HANDLE_INVALID);
    }

    for(iClient = 0; iClient != dObj->nClientsMax; iClient++)
    {
        clientObj = &((DRV_SPI_CLIENT_OBJ *)dObj->clientObjPool)[iClient];

        if(clientObj->inUse == false)
        {
            /* This means we have a free client object to use */
            clientObj->inUse = true;

            if(((uint32_t)ioIntent & (uint32_t)DRV_IO_INTENT_EXCLUSIVE) != 0U)
            {
                /* Set the driver exclusive flag */
                dObj->isExclusive = true;
            }

            dObj->nClients ++;

            /* Generate the client handle */
            clientObj->clientHandle = (DRV_HANDLE)lDRV_SPI_MAKE_HANDLE(dObj->spiTokenCount,
                    (uint8_t)drvIndex, (uint8_t)iClient);

            /* Increment the instance specific token counter */
            dObj->spiTokenCount = lDRV_SPI_UPDATE_TOKEN(dObj->spiTokenCount);

            /* We have found a client object, now release the mutex */
            (void) OSAL_MUTEX_Unlock(&(dObj->mutexClientObjects));

            temp = (uint32_t)ioIntent | (uint32_t)DRV_IO_INTENT_NONBLOCKING;
            /* This driver will always work in Non-Blocking mode */
            clientObj->ioIntent             = (DRV_IO_INTENT)(temp);

            /* Initialize other elements in Client Object */
            clientObj->eventHandler         = NULL;
            clientObj->context              = 0U;
            clientObj->setup.chipSelect     = SYS_PORT_PIN_NONE;
            clientObj->setupChanged         = false;
            clientObj->drvIndex             = drvIndex;

            return clientObj->clientHandle;
        }
    }

    /* Could not find a client object. Release the mutex and return with an invalid handle. */
    (void) OSAL_MUTEX_Unlock(&(dObj->mutexClientObjects));

    return DRV_HANDLE_INVALID;
}

void DRV_SPI_Close( DRV_HANDLE handle )
{
    /* This function closes the client, The client objects are deallocated and
     * returned to the free pool. */

    DRV_SPI_CLIENT_OBJ* clientObj;
    DRV_SPI_OBJ* dObj;

    /* Validate the driver handle */
    clientObj = lDRV_SPI_DriverHandleValidate(handle);

    if(clientObj == NULL)
    {
        SYS_DEBUG_MESSAGE(SYS_ERROR_ERROR, "Invalid Driver Handle");
        return;
    }

    dObj = (DRV_SPI_OBJ *)&gDrvSPIObj[clientObj->drvIndex];

    /* Guard against multiple threads trying to open/close the driver */
    if (OSAL_MUTEX_Lock(&dObj->mutexClientObjects , OSAL_WAIT_FOREVER ) == OSAL_RESULT_FAIL)
    {
        SYS_DEBUG_MESSAGE(SYS_ERROR_ERROR, "Failed to get client mutex lock");
        return;
    }
    /* We will be removing the transfers queued by the client. Guard the linked list
     * against interrupts */
    if(lDRV_SPI_ResourceLock(dObj) == false)
    {
        SYS_DEBUG_MESSAGE(SYS_ERROR_ERROR, "Failed to get resource lock");
        return;
    }

    /* Release the mutex if the client being closed was using the driver in exclusive mode */
    if (dObj->exclusiveUseClientHandle == handle)
    {
        dObj->drvInExclusiveMode = false;
        dObj->exclusiveUseCntr = 0;
        dObj->exclusiveUseClientHandle = DRV_HANDLE_INVALID;

        /* Release the exclusive use mutex (if held by the client) */
        (void) OSAL_MUTEX_Unlock( &dObj->mutexExclusiveUse);
    }

    /* Remove all buffers that this client owns from the driver queue */
    lDRV_SPI_RemoveClientTransfersFromList(dObj, clientObj);

    lDRV_SPI_ResourceUnlock(dObj);

    /* Reduce the number of clients */
    dObj->nClients--;

    /* Reset the exclusive flag */
    dObj->isExclusive = false;

    /* Invalidate the client handle */
    clientObj->clientHandle = DRV_HANDLE_INVALID;

    /* De-allocate the client object */
    clientObj->inUse = false;

    (void) OSAL_MUTEX_Unlock(&(dObj->mutexClientObjects));

    return;
}


void DRV_SPI_TransferEventHandlerSet(
    const DRV_HANDLE handle,
    const DRV_SPI_TRANSFER_EVENT_HANDLER eventHandler,
    uintptr_t context
)
{
    DRV_SPI_CLIENT_OBJ* clientObj = NULL;
    DRV_SPI_OBJ* dObj = (DRV_SPI_OBJ*)NULL;

    /* Validate the driver handle */
    clientObj = lDRV_SPI_DriverHandleValidate(handle);

    if(clientObj == NULL)
    {
        SYS_DEBUG_MESSAGE(SYS_ERROR_ERROR, "Invalid Driver Handle");
        return;
    }

    dObj = (DRV_SPI_OBJ *)&gDrvSPIObj[clientObj->drvIndex];

    if(lDRV_SPI_ResourceLock(dObj) == false)
    {
        SYS_DEBUG_MESSAGE(SYS_ERROR_ERROR, "Failed to get resource lock");
        return;
    }

    /* Save the event handler and context */
    clientObj->eventHandler = eventHandler;
    clientObj->context = context;

    lDRV_SPI_ResourceUnlock(dObj);
}

bool DRV_SPI_TransferSetup (
    const DRV_HANDLE handle,
    DRV_SPI_TRANSFER_SETUP* setup
)
{
    DRV_SPI_CLIENT_OBJ* clientObj = NULL;
    bool isSuccess = false;

    /* Validate the driver handle */
    clientObj = lDRV_SPI_DriverHandleValidate(handle);

    if((clientObj != NULL) && (setup != NULL))
    {
        /* Save the required setup in client object which can be used while
        processing queue requests. */
        clientObj->setup = *setup;

        /* Update the flag denoting that setup has been changed dynamically */
        clientObj->setupChanged = true;

        isSuccess = true;
    }
    return isSuccess;
}

void DRV_SPI_WriteReadTransferAdd (
    const DRV_HANDLE handle,
    void* pTransmitData,
    size_t txSize,
    void* pReceiveData,
    size_t rxSize,
    DRV_SPI_TRANSFER_HANDLE* const transferHandle
)
{
    DRV_SPI_CLIENT_OBJ* clientObj = (DRV_SPI_CLIENT_OBJ*)NULL;
    DRV_SPI_OBJ* dObj = (DRV_SPI_OBJ*)NULL;
    DRV_SPI_TRANSFER_OBJ* transferObj = (DRV_SPI_TRANSFER_OBJ*)NULL;

    if (transferHandle == NULL)
    {
        return;
    }

    *transferHandle = DRV_SPI_TRANSFER_HANDLE_INVALID;

    /* Validate the driver handle */
    clientObj = lDRV_SPI_DriverHandleValidate(handle);
    if (clientObj == NULL)
    {
        return;
    }

    if( ((txSize > 0U) && (pTransmitData != NULL)) || ((rxSize > 0U) && (pReceiveData != NULL)) )
    {
        dObj = (DRV_SPI_OBJ *)&gDrvSPIObj[clientObj->drvIndex];

        if (dObj->drvInExclusiveMode == true)
        {
            if (dObj->exclusiveUseClientHandle != handle)
            {
                return;
            }
        }

        if(lDRV_SPI_ResourceLock(dObj) == false)
        {
            SYS_DEBUG_MESSAGE(SYS_ERROR_ERROR, "Failed to get resource lock");
            return;
        }

        /* Get a free transfer object */
        transferObj = lDRV_SPI_FreeTransferObjGet(clientObj);

        if (transferObj == NULL)
        {
            /* This means we could not find a buffer. This will happen if the the
             * transfer queue size parameter is configured to be less */

            SYS_DEBUG_MESSAGE(SYS_ERROR_ERROR, "Insufficient Queue Depth");
            lDRV_SPI_ResourceUnlock(dObj);
            return;
        }

        /* Configure the object */
        transferObj->pReceiveData   = pReceiveData;
        transferObj->pTransmitData  = pTransmitData;
        transferObj->currentState   = DRV_SPI_TRANSFER_OBJ_IS_IN_QUEUE;
        transferObj->event          = DRV_SPI_TRANSFER_EVENT_PENDING;
        transferObj->clientHandle   = handle;

        if (clientObj->setup.dataBits == DRV_SPI_DATA_BITS_8)
        {
            transferObj->txSize = txSize;
            transferObj->rxSize = rxSize;
        }
        else if (clientObj->setup.dataBits <= DRV_SPI_DATA_BITS_16)
        {
            /* Both SPI and DMA PLIB expect size to be in terms of bytes */
            transferObj->txSize = txSize << 1;
            transferObj->rxSize = rxSize << 1;
        }
        else
        {
            /* Both SPI and DMA PLIB expect size to be in terms of bytes */
            transferObj->txSize = txSize << 2;
            transferObj->rxSize = rxSize << 2;
        }

        /* Update the unique transfer handle in output parameter.This handle can
         * be used by user to poll the status of transfer operation */
        *transferHandle = transferObj->transferHandle;

        /* Add the buffer object to the transfer buffer list */
        if (lDRV_SPI_TransferObjAddToList(dObj, transferObj) == true)
        {
            transferObj->currentState = DRV_SPI_TRANSFER_OBJ_IS_PROCESSING;

             /* This is the first request in the queue, hence initiate a transfer */
            lDRV_SPI_UpdateTransferSetupAndAssertCS(transferObj);

            if((dObj->txDMAChannel != SYS_DMA_CHANNEL_NONE) && (dObj->rxDMAChannel != SYS_DMA_CHANNEL_NONE))
            {
                lDRV_SPI_StartDMATransfer(transferObj);
            }
            else
            {
                (void) dObj->spiPlib->writeRead(transferObj->pTransmitData, transferObj->txSize, transferObj->pReceiveData, transferObj->rxSize);
            }
        }

        lDRV_SPI_ResourceUnlock(dObj);
    }
}

void DRV_SPI_WriteTransferAdd (
    const   DRV_HANDLE  handle,
    void*   pTransmitData,
    size_t  txSize,
    DRV_SPI_TRANSFER_HANDLE* const transferHandle
)
{
    DRV_SPI_WriteReadTransferAdd(handle, pTransmitData, txSize, NULL, 0, transferHandle);
}

void DRV_SPI_ReadTransferAdd (
    const   DRV_HANDLE  handle,
    void*   pReceiveData,
    size_t  rxSize,
    DRV_SPI_TRANSFER_HANDLE* const transferHandle
)
{
    DRV_SPI_WriteReadTransferAdd(handle, NULL, 0, pReceiveData, rxSize, transferHandle);
}

DRV_SPI_TRANSFER_EVENT DRV_SPI_TransferStatusGet(const DRV_SPI_TRANSFER_HANDLE transferHandle)
{
    DRV_SPI_OBJ* dObj = NULL;
    uint32_t drvInstance = 0;
    uint8_t transferIndex;

    /* Extract driver instance value from the transfer handle */
    drvInstance = ((transferHandle & DRV_SPI_INSTANCE_MASK) >> 8);

    if(drvInstance >= DRV_SPI_INSTANCES_NUMBER)
    {
        SYS_DEBUG_MESSAGE(SYS_ERROR_ERROR, "Transfer Handle Invalid");
        return DRV_SPI_TRANSFER_EVENT_HANDLE_INVALID;
    }

    dObj = (DRV_SPI_OBJ*)&gDrvSPIObj[drvInstance];

    /* Extract transfer buffer index value from the transfer handle */
    transferIndex = (uint8_t)(transferHandle & DRV_SPI_INDEX_MASK);

    /* Validate the transferIndex and corresponding request */
    if(transferIndex >= dObj->transferObjPoolSize)
    {
        SYS_DEBUG_MESSAGE(SYS_ERROR_ERROR, "Transfer Handle Invalid");
        return DRV_SPI_TRANSFER_EVENT_HANDLE_INVALID;
    }
    else if(transferHandle != dObj->transferObjPool[transferIndex].transferHandle)
    {
        //SYS_DEBUG_MESSAGE(SYS_ERROR_ERROR, "Transfer Handle Expired");
        return DRV_SPI_TRANSFER_EVENT_HANDLE_EXPIRED;
    }
    else
    {
        return dObj->transferObjPool[transferIndex].event;
    }
}

bool DRV_SPI_Lock( const DRV_HANDLE handle, bool lock )
{
    return DRV_SPI_ExclusiveUse(handle, lock );
}
