MajenkoProjects/TerminalServer/TerminalServer/Firmware/src/config/default/peripheral/uart/plib_uart1.c

/*******************************************************************************
  UART1 PLIB

  Company:
    Microchip Technology Inc.

  File Name:
    plib_uart1.c

  Summary:
    UART1 PLIB Implementation File

  Description:
    None

*******************************************************************************/

/*******************************************************************************
* Copyright (C) 2019 Microchip Technology Inc. and its subsidiaries.
*
* Subject to your compliance with these terms, you may use Microchip software
* and any derivatives exclusively with Microchip products. It is your
* responsibility to comply with third party license terms applicable to your
* use of third party software (including open source software) that may
* accompany Microchip software.
*
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
* IN NO EVENT WILL MICROCHIP BE LIABLE FOR ANY INDIRECT, SPECIAL, PUNITIVE,
* INCIDENTAL OR CONSEQUENTIAL LOSS, DAMAGE, COST OR EXPENSE OF ANY KIND
* WHATSOEVER RELATED TO THE SOFTWARE, HOWEVER CAUSED, EVEN IF MICROCHIP HAS
* BEEN ADVISED OF THE POSSIBILITY OR THE DAMAGES ARE FORESEEABLE. TO THE
* FULLEST EXTENT ALLOWED BY LAW, MICROCHIP'S TOTAL LIABILITY ON ALL CLAIMS IN
* ANY WAY RELATED TO THIS SOFTWARE WILL NOT EXCEED THE AMOUNT OF FEES, IF ANY,
* THAT YOU HAVE PAID DIRECTLY TO MICROCHIP FOR THIS SOFTWARE.
*******************************************************************************/

#include "device.h"
#include "plib_uart1.h"
#include "interrupts.h"

// *****************************************************************************
// *****************************************************************************
// Section: UART1 Implementation
// *****************************************************************************
// *****************************************************************************

static volatile UART_RING_BUFFER_OBJECT uart1Obj;

#define UART1_READ_BUFFER_SIZE      (8U)
#define UART1_READ_BUFFER_SIZE_9BIT (8U >> 1)
#define UART1_RX_INT_DISABLE()      IEC0CLR = _IEC0_U1RXIE_MASK;
#define UART1_RX_INT_ENABLE()       IEC0SET = _IEC0_U1RXIE_MASK;

static volatile uint8_t UART1_ReadBuffer[UART1_READ_BUFFER_SIZE];

#define UART1_WRITE_BUFFER_SIZE      (128U)
#define UART1_WRITE_BUFFER_SIZE_9BIT (128U >> 1)
#define UART1_TX_INT_DISABLE()       IEC0CLR = _IEC0_U1TXIE_MASK;
#define UART1_TX_INT_ENABLE()        IEC0SET = _IEC0_U1TXIE_MASK;

static volatile uint8_t UART1_WriteBuffer[UART1_WRITE_BUFFER_SIZE];

#define UART1_IS_9BIT_MODE_ENABLED()    ( (U1MODE) & (_U1MODE_PDSEL0_MASK | _U1MODE_PDSEL1_MASK)) == (_U1MODE_PDSEL0_MASK | _U1MODE_PDSEL1_MASK) ? true:false

static void UART1_ErrorClear( void )
{
    UART_ERROR errors = UART_ERROR_NONE;
    uint8_t dummyData = 0u;

    errors = (UART_ERROR)(U1STA & (_U1STA_OERR_MASK | _U1STA_FERR_MASK | _U1STA_PERR_MASK));

    if(errors != UART_ERROR_NONE)
    {
        /* If it's a overrun error then clear it to flush FIFO */
        if((U1STA & _U1STA_OERR_MASK) != 0U)
        {
            U1STACLR = _U1STA_OERR_MASK;
        }

        /* Read existing error bytes from FIFO to clear parity and framing error flags */
        while((U1STA & _U1STA_URXDA_MASK) != 0U)
        {
            dummyData = (uint8_t)U1RXREG;
        }

        /* Clear error interrupt flag */
        IFS0CLR = _IFS0_U1EIF_MASK;

        /* Clear up the receive interrupt flag so that RX interrupt is not
         * triggered for error bytes */
        IFS0CLR = _IFS0_U1RXIF_MASK;

    }

    // Ignore the warning
    (void)dummyData;
}

void UART1_Initialize( void )
{
    /* Set up UxMODE bits */
    /* STSEL  = 0 */
    /* PDSEL = 0 */

    U1MODE = 0x8;

    /* Enable UART1 Receiver and Transmitter */
    U1STASET = (_U1STA_UTXEN_MASK | _U1STA_URXEN_MASK | _U1STA_UTXISEL1_MASK );

    /* BAUD Rate register Setup */
    U1BRG = 173;

    /* Disable Interrupts */
    IEC0CLR = _IEC0_U1EIE_MASK;

    IEC0CLR = _IEC0_U1RXIE_MASK;

    IEC0CLR = _IEC0_U1TXIE_MASK;

    /* Initialize instance object */
    uart1Obj.rdCallback = NULL;
    uart1Obj.rdInIndex = 0;
    uart1Obj.rdOutIndex = 0;
    uart1Obj.isRdNotificationEnabled = false;
    uart1Obj.isRdNotifyPersistently = false;
    uart1Obj.rdThreshold = 0;

    uart1Obj.wrCallback = NULL;
    uart1Obj.wrInIndex = 0;
    uart1Obj.wrOutIndex = 0;
    uart1Obj.isWrNotificationEnabled = false;
    uart1Obj.isWrNotifyPersistently = false;
    uart1Obj.wrThreshold = 0;

    uart1Obj.errors = UART_ERROR_NONE;

    if (UART1_IS_9BIT_MODE_ENABLED())
    {
        uart1Obj.rdBufferSize = UART1_READ_BUFFER_SIZE_9BIT;
        uart1Obj.wrBufferSize = UART1_WRITE_BUFFER_SIZE_9BIT;
    }
    else
    {
        uart1Obj.rdBufferSize = UART1_READ_BUFFER_SIZE;
        uart1Obj.wrBufferSize = UART1_WRITE_BUFFER_SIZE;
    }


    /* Turn ON UART1 */
    U1MODESET = _U1MODE_ON_MASK;

    /* Enable UART1_FAULT Interrupt */
    IEC0SET = _IEC0_U1EIE_MASK;

    /* Enable UART1_RX Interrupt */
    IEC0SET = _IEC0_U1RXIE_MASK;
}

bool UART1_SerialSetup( UART_SERIAL_SETUP *setup, uint32_t srcClkFreq )
{
    bool status = false;
    uint32_t baud;
    uint32_t status_ctrl;
    uint32_t uxbrg = 0;

    if (setup != NULL)
    {
        baud = setup->baudRate;

        if ((baud == 0U) || ((setup->dataWidth == UART_DATA_9_BIT) && (setup->parity != UART_PARITY_NONE)))
        {
            return status;
        }

        if(srcClkFreq == 0U)
        {
            srcClkFreq = UART1_FrequencyGet();
        }

        /* Calculate BRG value */
        uxbrg = (((srcClkFreq >> 2) + (baud >> 1)) / baud);

        /* Check if the baud value can be set with low baud settings */
        if (uxbrg < 1U)
        {
            return status;
        }

        uxbrg -= 1U;

        if (uxbrg > UINT16_MAX)
        {
            return status;
        }

        /* Turn OFF UART1. Save UTXEN, URXEN and UTXBRK bits as these are cleared upon disabling UART */

        status_ctrl = U1STA & (_U1STA_UTXEN_MASK | _U1STA_URXEN_MASK | _U1STA_UTXBRK_MASK);

        U1MODECLR = _U1MODE_ON_MASK;

        if(setup->dataWidth == UART_DATA_9_BIT)
        {
            /* Configure UART1 mode */
            U1MODE = (U1MODE & (~_U1MODE_PDSEL_MASK)) | setup->dataWidth;
        }
        else
        {
            /* Configure UART1 mode */
            U1MODE = (U1MODE & (~_U1MODE_PDSEL_MASK)) | setup->parity;
        }

        /* Configure UART1 mode */
        U1MODE = (U1MODE & (~_U1MODE_STSEL_MASK)) | setup->stopBits;

        /* Configure UART1 Baud Rate */
        U1BRG = uxbrg;

        if (UART1_IS_9BIT_MODE_ENABLED())
        {
            uart1Obj.rdBufferSize = UART1_READ_BUFFER_SIZE_9BIT;
            uart1Obj.wrBufferSize = UART1_WRITE_BUFFER_SIZE_9BIT;
        }
        else
        {
            uart1Obj.rdBufferSize = UART1_READ_BUFFER_SIZE;
            uart1Obj.wrBufferSize = UART1_WRITE_BUFFER_SIZE;
        }

        U1MODESET = _U1MODE_ON_MASK;

        /* Restore UTXEN, URXEN and UTXBRK bits. */
        U1STASET = status_ctrl;

        status = true;
    }

    return status;
}

/* This routine is only called from ISR. Hence do not disable/enable USART interrupts. */
static inline bool UART1_RxPushByte(uint16_t rdByte)
{
    uint32_t tempInIndex;
    bool isSuccess = false;
    uint32_t rdInIdx;

    tempInIndex = uart1Obj.rdInIndex + 1U;

    if (tempInIndex >= uart1Obj.rdBufferSize)
    {
        tempInIndex = 0U;
    }

    if (tempInIndex == uart1Obj.rdOutIndex)
    {
        /* Queue is full - Report it to the application. Application gets a chance to free up space by reading data out from the RX ring buffer */
        if(uart1Obj.rdCallback != NULL)
        {
            uintptr_t rdContext = uart1Obj.rdContext;

            uart1Obj.rdCallback(UART_EVENT_READ_BUFFER_FULL, rdContext);

            /* Read the indices again in case application has freed up space in RX ring buffer */
            tempInIndex = uart1Obj.rdInIndex + 1U;

            if (tempInIndex >= uart1Obj.rdBufferSize)
            {
                tempInIndex = 0U;
            }
        }
    }

    /* Attempt to push the data into the ring buffer */
    if (tempInIndex != uart1Obj.rdOutIndex)
    {
        uint32_t rdInIndex = uart1Obj.rdInIndex;

        if (UART1_IS_9BIT_MODE_ENABLED())
        {
            rdInIdx = uart1Obj.rdInIndex << 1U;
            UART1_ReadBuffer[rdInIdx] = (uint8_t)rdByte;
            UART1_ReadBuffer[rdInIdx + 1U] = (uint8_t)(rdByte >> 8U);
        }
        else
        {
            UART1_ReadBuffer[rdInIndex] = (uint8_t)rdByte;
        }

        uart1Obj.rdInIndex = tempInIndex;

        isSuccess = true;
    }
    else
    {
        /* Queue is full. Data will be lost. */
    }

    return isSuccess;
}

/* This routine is only called from ISR. Hence do not disable/enable USART interrupts. */
static void UART1_ReadNotificationSend(void)
{
    uint32_t nUnreadBytesAvailable;

    if (uart1Obj.isRdNotificationEnabled == true)
    {
        nUnreadBytesAvailable = UART1_ReadCountGet();

        if(uart1Obj.rdCallback != NULL)
        {
            uintptr_t rdContext = uart1Obj.rdContext;

            if (uart1Obj.isRdNotifyPersistently == true)
            {
                if (nUnreadBytesAvailable >= uart1Obj.rdThreshold)
                {
                    uart1Obj.rdCallback(UART_EVENT_READ_THRESHOLD_REACHED, rdContext);
                }
            }
            else
            {
                if (nUnreadBytesAvailable == uart1Obj.rdThreshold)
                {
                    uart1Obj.rdCallback(UART_EVENT_READ_THRESHOLD_REACHED, rdContext);
                }
            }
        }
    }
}

size_t UART1_Read(uint8_t* pRdBuffer, const size_t size)
{
    size_t nBytesRead = 0;
    uint32_t rdOutIndex = 0;
    uint32_t rdInIndex = 0;
    uint32_t rdOut16Idx;
    uint32_t nBytesRead16Idx;

    /* Take a snapshot of indices to avoid creation of critical section */
    rdOutIndex = uart1Obj.rdOutIndex;
    rdInIndex = uart1Obj.rdInIndex;

    while (nBytesRead < size)
    {
        if (rdOutIndex != rdInIndex)
        {
            if (UART1_IS_9BIT_MODE_ENABLED())
            {
                rdOut16Idx = rdOutIndex << 1U;
                nBytesRead16Idx = nBytesRead << 1U;

                pRdBuffer[nBytesRead16Idx] = UART1_ReadBuffer[rdOut16Idx];
                pRdBuffer[nBytesRead16Idx + 1U] = UART1_ReadBuffer[rdOut16Idx + 1U];
            }
            else
            {
                pRdBuffer[nBytesRead] = UART1_ReadBuffer[rdOutIndex];
            }
            nBytesRead++;
            rdOutIndex++;

            if (rdOutIndex >= uart1Obj.rdBufferSize)
            {
                rdOutIndex = 0U;
            }
        }
        else
        {
            /* No more data available in the RX buffer */
            break;
        }
    }

    uart1Obj.rdOutIndex = rdOutIndex;

    return nBytesRead;
}

size_t UART1_ReadCountGet(void)
{
    size_t nUnreadBytesAvailable;
    uint32_t rdInIndex;
    uint32_t rdOutIndex;

    /* Take a snapshot of indices to avoid processing in critical section */
    rdInIndex = uart1Obj.rdInIndex;
    rdOutIndex = uart1Obj.rdOutIndex;

    if ( rdInIndex >=  rdOutIndex)
    {
        nUnreadBytesAvailable =  rdInIndex -  rdOutIndex;
    }
    else
    {
        nUnreadBytesAvailable =  (uart1Obj.rdBufferSize -  rdOutIndex) + rdInIndex;
    }

    return nUnreadBytesAvailable;
}

size_t UART1_ReadFreeBufferCountGet(void)
{
    return (uart1Obj.rdBufferSize - 1U) - UART1_ReadCountGet();
}

size_t UART1_ReadBufferSizeGet(void)
{
    return (uart1Obj.rdBufferSize - 1U);
}

bool UART1_ReadNotificationEnable(bool isEnabled, bool isPersistent)
{
    bool previousStatus = uart1Obj.isRdNotificationEnabled;

    uart1Obj.isRdNotificationEnabled = isEnabled;

    uart1Obj.isRdNotifyPersistently = isPersistent;

    return previousStatus;
}

void UART1_ReadThresholdSet(uint32_t nBytesThreshold)
{
    if (nBytesThreshold > 0U)
    {
        uart1Obj.rdThreshold = nBytesThreshold;
    }
}

void UART1_ReadCallbackRegister( UART_RING_BUFFER_CALLBACK callback, uintptr_t context)
{
    uart1Obj.rdCallback = callback;

    uart1Obj.rdContext = context;
}

/* This routine is only called from ISR. Hence do not disable/enable USART interrupts. */
static bool UART1_TxPullByte(void* pWrData)
{
    bool isSuccess = false;
    uint32_t wrOutIndex = uart1Obj.wrOutIndex;
    uint32_t wrInIndex = uart1Obj.wrInIndex;
    uint32_t wrOut16Idx;
    uint8_t* pWrByte = (uint8_t*)pWrData;

    if (wrOutIndex != wrInIndex)
    {
        if (UART1_IS_9BIT_MODE_ENABLED())
        {
            wrOut16Idx = wrOutIndex << 1U;
            pWrByte[0] = UART1_WriteBuffer[wrOut16Idx];
            pWrByte[1] = UART1_WriteBuffer[wrOut16Idx + 1U];
        }
        else
        {
            *pWrByte = UART1_WriteBuffer[wrOutIndex];
        }
        wrOutIndex++;

        if (wrOutIndex >= uart1Obj.wrBufferSize)
        {
            wrOutIndex = 0U;
        }

        uart1Obj.wrOutIndex = wrOutIndex;

        isSuccess = true;
    }

    return isSuccess;
}

static inline bool UART1_TxPushByte(uint16_t wrByte)
{
    uint32_t tempInIndex;
    bool isSuccess = false;
    uint32_t wrOutIndex = uart1Obj.wrOutIndex;
    uint32_t wrInIndex = uart1Obj.wrInIndex;
    uint32_t wrIn16Idx;

    tempInIndex = wrInIndex + 1U;

    if (tempInIndex >= uart1Obj.wrBufferSize)
    {
        tempInIndex = 0U;
    }
    if (tempInIndex != wrOutIndex)
    {
        if (UART1_IS_9BIT_MODE_ENABLED())
        {
            wrIn16Idx = wrInIndex << 1U;
            UART1_WriteBuffer[wrIn16Idx] = (uint8_t)wrByte;
            UART1_WriteBuffer[wrIn16Idx + 1U] = (uint8_t)(wrByte >> 8U);
        }
        else
        {
            UART1_WriteBuffer[wrInIndex] = (uint8_t)wrByte;
        }

        uart1Obj.wrInIndex = tempInIndex;

        isSuccess = true;
    }
    else
    {
        /* Queue is full. Report Error. */
    }

    return isSuccess;
}

/* This routine is only called from ISR. Hence do not disable/enable USART interrupts. */
static void UART1_WriteNotificationSend(void)
{
    uint32_t nFreeWrBufferCount;

    if (uart1Obj.isWrNotificationEnabled == true)
    {
        nFreeWrBufferCount = UART1_WriteFreeBufferCountGet();

        if(uart1Obj.wrCallback != NULL)
        {
            uintptr_t wrContext = uart1Obj.wrContext;

            if (uart1Obj.isWrNotifyPersistently == true)
            {
                if (nFreeWrBufferCount >= uart1Obj.wrThreshold)
                {
                    uart1Obj.wrCallback(UART_EVENT_WRITE_THRESHOLD_REACHED, wrContext);
                }
            }
            else
            {
                if (nFreeWrBufferCount == uart1Obj.wrThreshold)
                {
                    uart1Obj.wrCallback(UART_EVENT_WRITE_THRESHOLD_REACHED, wrContext);
                }
            }
        }
    }
}

static size_t UART1_WritePendingBytesGet(void)
{
    size_t nPendingTxBytes;

    /* Take a snapshot of indices to avoid processing in critical section */

    uint32_t wrOutIndex = uart1Obj.wrOutIndex;
    uint32_t wrInIndex = uart1Obj.wrInIndex;

    if ( wrInIndex >=  wrOutIndex)
    {
        nPendingTxBytes =  wrInIndex - wrOutIndex;
    }
    else
    {
        nPendingTxBytes =  (uart1Obj.wrBufferSize -  wrOutIndex) + wrInIndex;
    }

    return nPendingTxBytes;
}

size_t UART1_WriteCountGet(void)
{
    size_t nPendingTxBytes;

    nPendingTxBytes = UART1_WritePendingBytesGet();

    return nPendingTxBytes;
}

size_t UART1_Write(uint8_t* pWrBuffer, const size_t size )
{
    size_t nBytesWritten  = 0;
    uint16_t halfWordData = 0U;

    while (nBytesWritten < size)
    {
        if (UART1_IS_9BIT_MODE_ENABLED())
        {
            halfWordData = pWrBuffer[(2U * nBytesWritten) + 1U];
            halfWordData <<= 8U;
            halfWordData |= pWrBuffer[(2U * nBytesWritten)];
            if (UART1_TxPushByte(halfWordData) == true)
            {
                nBytesWritten++;
            }
            else
            {
                /* Queue is full, exit the loop */
                break;
            }
        }
        else
        {
            if (UART1_TxPushByte(pWrBuffer[nBytesWritten]) == true)
            {
                nBytesWritten++;
            }
            else
            {
                /* Queue is full, exit the loop */
                break;
            }
        }

    }

    /* Check if any data is pending for transmission */
    if (UART1_WritePendingBytesGet() > 0U)
    {
        /* Enable TX interrupt as data is pending for transmission */
        UART1_TX_INT_ENABLE();
    }

    return nBytesWritten;
}

size_t UART1_WriteFreeBufferCountGet(void)
{
    return (uart1Obj.wrBufferSize - 1U) - UART1_WriteCountGet();
}

size_t UART1_WriteBufferSizeGet(void)
{
    return (uart1Obj.wrBufferSize - 1U);
}

bool UART1_TransmitComplete( void )
{
    bool transmitcompltecheck = false;
    if((U1STA & _U1STA_TRMT_MASK) != 0U)
    {
        transmitcompltecheck = true;
    }
    return transmitcompltecheck;
}

bool UART1_WriteNotificationEnable(bool isEnabled, bool isPersistent)
{
    bool previousStatus = uart1Obj.isWrNotificationEnabled;

    uart1Obj.isWrNotificationEnabled = isEnabled;

    uart1Obj.isWrNotifyPersistently = isPersistent;

    return previousStatus;
}

void UART1_WriteThresholdSet(uint32_t nBytesThreshold)
{
    if (nBytesThreshold > 0U)
    {
        uart1Obj.wrThreshold = nBytesThreshold;
    }
}

void UART1_WriteCallbackRegister( UART_RING_BUFFER_CALLBACK callback, uintptr_t context)
{
    uart1Obj.wrCallback = callback;

    uart1Obj.wrContext = context;
}

UART_ERROR UART1_ErrorGet( void )
{
    UART_ERROR errors = uart1Obj.errors;

    uart1Obj.errors = UART_ERROR_NONE;

    /* All errors are cleared, but send the previous error state */
    return errors;
}

bool UART1_AutoBaudQuery( void )
{
    bool autobaudq_check = false;
    if((U1MODE & _U1MODE_ABAUD_MASK) != 0U)
    {
         autobaudq_check = true;
    }
     return autobaudq_check;
}

void UART1_AutoBaudSet( bool enable )
{
    if( enable == true )
    {
        U1MODESET = _U1MODE_ABAUD_MASK;
    }

    /* Turning off ABAUD if it was on can lead to unpredictable behavior, so that
       direction of control is not allowed in this function.                      */
}

static void __attribute__((used)) UART1_FAULT_InterruptHandler (void)
{
    /* Save the error to be reported later */
    uart1Obj.errors = (UART_ERROR)(U1STA & (_U1STA_OERR_MASK | _U1STA_FERR_MASK | _U1STA_PERR_MASK));

    UART1_ErrorClear();

    /* Client must call UARTx_ErrorGet() function to clear the errors */
    if( uart1Obj.rdCallback != NULL )
    {
        uintptr_t rdContext = uart1Obj.rdContext;

        uart1Obj.rdCallback(UART_EVENT_READ_ERROR, rdContext);
    }
}

static void __attribute__((used)) UART1_RX_InterruptHandler (void)
{
    /* Keep reading until there is a character availabe in the RX FIFO */
    while((U1STA & _U1STA_URXDA_MASK) == _U1STA_URXDA_MASK)
    {
        if (UART1_RxPushByte( (uint16_t )(U1RXREG) ) == true)
        {
            UART1_ReadNotificationSend();
        }
        else
        {
            /* UART RX buffer is full */
        }
    }

    /* Clear UART1 RX Interrupt flag */
    IFS0CLR = _IFS0_U1RXIF_MASK;
}

static void __attribute__((used)) UART1_TX_InterruptHandler (void)
{
    uint16_t wrByte;

    /* Check if any data is pending for transmission */
    if (UART1_WritePendingBytesGet() > 0U)
    {
        /* Keep writing to the TX FIFO as long as there is space */
        while((U1STA & _U1STA_UTXBF_MASK) == 0U)
        {
            if (UART1_TxPullByte(&wrByte) == true)
            {
                if (UART1_IS_9BIT_MODE_ENABLED())
                {
                    U1TXREG = wrByte;
                }
                else
                {
                    U1TXREG = (uint8_t)wrByte;
                }

                /* Send notification */
                UART1_WriteNotificationSend();
            }
            else
            {
                /* Nothing to transmit. Disable the data register empty interrupt. */
                UART1_TX_INT_DISABLE();
                break;
            }
        }

        /* Clear UART1TX Interrupt flag */
        IFS0CLR = _IFS0_U1TXIF_MASK;
    }
    else
    {
        /* Nothing to transmit. Disable the data register empty interrupt. */
        UART1_TX_INT_DISABLE();

        /* Clear UART1TX Interrupt flag */
        IFS0CLR = _IFS0_U1TXIF_MASK;
    }
}

void __attribute__((used)) UART_1_InterruptHandler (void)
{
    uint32_t temp = IEC0;
    /* Call Error handler if Error interrupt flag is set */
    if (((IFS0 & _IFS0_U1EIF_MASK) != 0U) && ((temp & _IEC0_U1EIE_MASK) != 0U))
    {
        UART1_FAULT_InterruptHandler();
    }
    temp = IEC0;
    /* Call RX handler if RX interrupt flag is set */
    if (((IFS0 & _IFS0_U1RXIF_MASK) != 0U) && ((temp & _IEC0_U1RXIE_MASK) != 0U))
    {
        UART1_RX_InterruptHandler();
    }
    temp = IEC0;
    /* Call TX handler if TX interrupt flag is set */
    if (((IFS0 & _IFS0_U1TXIF_MASK) != 0U) && ((temp & _IEC0_U1TXIE_MASK) != 0U))
    {
        UART1_TX_InterruptHandler();
    }

}
