MajenkoProjects/TerminalServer/TerminalServer/Firmware/src/config/default/driver/sdspi/src/drv_sdspi_local.h

/*******************************************************************************
  SD Card (SPI) Driver Local Data Structures

  Company:
    Microchip Technology Inc.

  File Name:
    drv_sdspi_local.h

  Summary:
    SD Card (SPI) Driver local declarations, structures and function prototypes.

  Description:
    This file contains the SD Card (SPI) Driver's local declarations and definitions.
*******************************************************************************/

//DOM-IGNORE-BEGIN
/*******************************************************************************
* Copyright (C) 2019 Microchip Technology Inc. and its subsidiaries.
*
* Subject to your compliance with these terms, you may use Microchip software
* and any derivatives exclusively with Microchip products. It is your
* responsibility to comply with third party license terms applicable to your
* use of third party software (including open source software) that may
* accompany Microchip software.
*
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
* IN NO EVENT WILL MICROCHIP BE LIABLE FOR ANY INDIRECT, SPECIAL, PUNITIVE,
* INCIDENTAL OR CONSEQUENTIAL LOSS, DAMAGE, COST OR EXPENSE OF ANY KIND
* WHATSOEVER RELATED TO THE SOFTWARE, HOWEVER CAUSED, EVEN IF MICROCHIP HAS
* BEEN ADVISED OF THE POSSIBILITY OR THE DAMAGES ARE FORESEEABLE. TO THE
* FULLEST EXTENT ALLOWED BY LAW, MICROCHIP'S TOTAL LIABILITY ON ALL CLAIMS IN
* ANY WAY RELATED TO THIS SOFTWARE WILL NOT EXCEED THE AMOUNT OF FEES, IF ANY,
* THAT YOU HAVE PAID DIRECTLY TO MICROCHIP FOR THIS SOFTWARE.
 *******************************************************************************/
//DOM-IGNORE-END

#ifndef DRV_SDSPI_LOCAL_H
#define DRV_SDSPI_LOCAL_H


// *****************************************************************************
// *****************************************************************************
// Section: File includes
// *****************************************************************************
// *****************************************************************************

#include <stdint.h>
#include <stdbool.h>
#include <stddef.h>

#include "configuration.h"
#include "driver/sdspi/drv_sdspi.h"
#include "osal/osal.h"

// *****************************************************************************
// *****************************************************************************
// Section: Helper Macros
// *****************************************************************************
// *****************************************************************************
/* Helper macros for the driver */


// *****************************************************************************
/* SDCARD Driver Buffer Handle Macros

  Summary:
    SDCARD driver Buffer Handle Macros

  Description:
    Buffer handle related utility macros. SDCARD driver buffer handle is a
    combination of buffer token and the buffer object index. The buffertoken
    is a 16 bit number that is incremented for every new write or erase request
    and is used along with the buffer object index to generate a new buffer
    handle for every request.

  Remarks:
    None
*/

#define DRV_SDSPI_INDEX_MASK                      (0x000000FFU)
#define DRV_SDSPI_INSTANCE_MASK                   (0x0000FF00U)
#define DRV_SDSPI_TOKEN_MAX                       (0xFFFFU)

#define DRV_SDSPI_FLOATING_BUS_TIMEOUT            (1000)
#define DRV_SDSPI_R1B_RESP_TIMEOUT                (100)

#define DRV_SDSPI_READ_TIMEOUT_IN_MS              (250)
#define DRV_SDSPI_WRITE_TIMEOUT_IN_MS             (250)

#define DRV_SDSPI_APP_CMD_RESP_TIMEOUT_IN_MS      (1000)
#define DRV_SDSPI_CSD_TOKEN_TIMEOUT_IN_MS         (1000)

#define DRV_SDSPI_COMMAND_RESPONSE_TRIES          (10)

// *****************************************************************************
// *****************************************************************************
// Section: SD Card constants
// *****************************************************************************
// *****************************************************************************
/* Constants used by SD Card (SPI) Driver */

// *****************************************************************************
/* SD Card initial speed

  Summary:
    Initial speed of the SPI communication.

  Description:
    This macro holds the value of the initial communication speed with SD card.
    SD card only work at <=400kHz SPI frequency during initialization.

  Remarks:
    None.
*/

#define DRV_SDSPI_SPI_INITIAL_SPEED                        400000


// *****************************************************************************
/* Count for 8 clock pulses

  Summary:
    Bytes count which should be passed to DRV_SPI_BufferReadAdd function to send
    8 clock pulses.

  Description:
    This macro holds the bytes count which should be passed to DRV_SPI_BufferReadAdd
    function to send 8 clock pulses. Sending one byte will send 8 clock pulses.


  Remarks:
    None.
*/

#define DRV_SDSPI_SEND_8_CLOCKS                                            1

// *****************************************************************************
/* No of bytes to be read for SD card CSD.

  Summary:
    Number of bytes to be read to get the SD card CSD.

  Description:
    This macro holds number of bytes to be read to get the SD card CSD.


  Remarks:
    None.
*/

#define DRV_SDSPI_CSD_READ_SIZE                                            20

// *****************************************************************************
/* No of bytes to be read for SD card CID.

  Summary:
    Number of bytes to be read to get the SD card CID.

  Description:
    This macro holds number of bytes to be read to get the SD card CID.


  Remarks:
    None.
*/
#define DRV_SDSPI_CID_READ_SIZE                                            20

// *****************************************************************************
/* SD card V2 device type.

  Summary:
    Holds the value to be checked against to state the device type is V2.

  Description:
    This macro holds value to be checked against to state the device type is V2.

  Remarks:
    None.
*/

#define DRV_SDSPI_CHECK_V2_DEVICE                        (0xC0U)


// *****************************************************************************
/* SD card sector size.

  Summary:
    Holds the SD card sector size.

  Description:
    This macro holds the SD card sector size.

  Remarks:
    None.
*/

#define DRV_SDSPI_MEDIA_BLOCK_SIZE                                         512


// *****************************************************************************
/* SD card transmit bit.

  Summary:
    Holds the SD card transmit bit position.

  Description:
    This macro holds the SD card transmit bit position.

  Remarks:
    None.
*/

#define DRV_SDSPI_TRANSMIT_SET                                        (0x40U)


// *****************************************************************************
/* Write response token bit mask.

  Summary:
    Bit mask to AND with the write token response byte from the media,

  Description:
    This macro holds the bit mask to AND with the write token response byte from
    the media to clear the don't care bits.

  Remarks:
    None.
*/

#define DRV_SDSPI_WRITE_RESPONSE_TOKEN_MASK                                (0x1FU)


// *****************************************************************************
/* SPI Bus floating

  Summary:
    This macro represents a floating SPI bus condition.

  Description:
    This macro represents a floating SPI bus condition.

  Remarks:
    None.
*/

#define DRV_SDSPI_MMC_FLOATING_BUS                                          (0xFFU)


// *****************************************************************************
/* SD card bad response

  Summary:
    This macro represents a bad SD card response byte.

  Description:
    This macro represents a bad SD card response byte.

  Remarks:
    None.
*/

#define DRV_SDSPI_MMC_BAD_RESPONSE          DRV_SDSPI_MMC_FLOATING_BUS


// *****************************************************************************
/* SD card start single block

  Summary:
    This macro represents an SD card start single data block token (used for
    single block writes).

  Description:
    This macro represents an SD card start single data block token (used for
    single block writes).

  Remarks:
    None.
*/

#define DRV_SDSPI_DATA_START_TOKEN                     (0xFEU)


// *****************************************************************************
/* SD card start multiple blocks

  Summary:
    This macro represents an SD card start multi-block data token (used for
    multi-block writes).

  Description:
    This macro represents an SD card start multi-block data token (used for
    multi-block writes).

  Remarks:
    None.
*/

#define DRV_SDSPI_DATA_START_MULTI_BLOCK_TOKEN         0xFC


// *****************************************************************************
/* SD card stop transmission

  Summary:
    This macro represents an SD card stop transmission token.  This is used when
    finishing a multi block write sequence.

  Description:
    This macro represents an SD card stop transmission token.  This is used when
    finishing a multi block write sequence.

  Remarks:
    None.
*/

#define DRV_SDSPI_DATA_STOP_TRAN_TOKEN                 0xFD


// *****************************************************************************
/* SD card data accepted token

  Summary:
    This macro represents an SD card data accepted token.

  Description:
    This macro represents an SD card data accepted token.

  Remarks:
    None.
*/

#define DRV_SDSPI_DATA_ACCEPTED                        (0x05U)


// *****************************************************************************
/* SD card R1 response end bit

  Summary:
    This macro holds a value to check R1 response end bit.

  Description:
    This macro holds a value to check R1 response end bit.

  Remarks:
    None.
*/

#define CMD_R1_END_BIT_SET                              (0x01U)


// *****************************************************************************
/* SD card initial packet size

  Summary:
    This macro holds SD card initial packet size.

  Description:
    This macro holds SD card initial packet size.

  Remarks:
    None.
*/

#define DRV_SDSPI_PACKET_SIZE                       6


// *****************************************************************************
/* SD card Media initialization array size

  Summary:
    This macro holds SD card Media initialization array size.

  Description:
    This macro holds SD card Media initialization array size.

  Remarks:
    None.
*/

#define MEDIA_INIT_ARRAY_SIZE                           (10U)

// *****************************************************************************
/* Dummy Buffer for DMA Transfers

  Summary:
    This macro holds the size of the dummy buffer used during DMA transfers.

  Description:
    This macro holds the size of the dummy buffer used during DMA transfers.

  Remarks:
    None.
*/

#define DMA_DUMMY_BUFFER_SIZE                           512


#if defined (DRV_SDSPI_ENABLE_WRITE_PROTECT_CHECK)
    #define DRV_SDSPI_EnableWriteProtectCheck() true
#else
    #define DRV_SDSPI_EnableWriteProtectCheck() false
#endif

// *****************************************************************************
// *****************************************************************************
// Section: SD Card Enumerations
// *****************************************************************************
// *****************************************************************************

typedef enum {
    TASK_STATE_IDLE,

    TASK_STATE_CARD_STATUS,

    TASK_STATE_CARD_COMMAND,

} DRV_SDSPI_TASK_STATE;

typedef enum
{
    DRV_SDSPI_OPERATION_TYPE_READ,

    DRV_SDSPI_OPERATION_TYPE_WRITE,

} DRV_SDSPI_OPERATION_TYPE;

typedef enum
{
    DRV_SDSPI_TRANSFER_OBJ_IS_FREE,

    DRV_SDSPI_TRANSFER_OBJ_IS_IN_QUEUE,

    DRV_SDSPI_TRANSFER_OBJ_IS_PROCESSING,

} DRV_SDSPI_TRANSFER_OBJ_STATE;

typedef enum
{
    /* All data was transferred successfully. */

    DRV_SDSPI_SPI_TRANSFER_STATUS_IN_PROGRESS,

    DRV_SDSPI_SPI_TRANSFER_STATUS_COMPLETE,

    /* There was an error while processing transfer request. */
    DRV_SDSPI_SPI_TRANSFER_STATUS_ERROR,

} DRV_SDSPI_SPI_TRANSFER_STATUS;

typedef enum
{
    /* Open the SPI Driver instance */
    DRV_SDSPI_TASK_OPEN_SPI,

    DRV_SDSPI_TASK_START_POLLING_TIMER,

    DRV_SDSPI_TASK_WAIT_POLLING_TIMER_EXPIRE,

    /* A device is attached */
    DRV_SDSPI_TASK_CHECK_DEVICE,

    /* If the card is attached, initialize */
    DRV_SDSPI_TASK_MEDIA_INIT,

    /* Idle State  */
    DRV_SDSPI_TASK_IDLE

} DRV_SDSPI_TASK_STATES;

typedef enum
{
    /* A device is attached */
    DRV_SDSPI_BUFFER_IO_CHECK_DEVICE,

    /* Process queue for Read and write */
    DRV_SDSPI_TASK_PROCESS_QUEUE,

    /* Process read */
    DRV_SDSPI_TASK_PROCESS_READ,

    /* Process write */
    DRV_SDSPI_TASK_PROCESS_WRITE,

    /* Wait for the SPI transaction to complete. */
    DRV_SDSPI_TASK_SPI_STATUS,

    /* Read the start token from the SD card. */
    DRV_SDSPI_TASK_RD_SRT_TKN,

    /* Check if the token received is correct */
    DRV_SDSPI_TASK_RD_SRT_TKN_STATUS,

    /* Read 512 bytes of data from the SD card. */
    DRV_SDSPI_TASK_READ_DATA,

    /* Read 2 bytes of crc data from the sd card. */
    DRV_SDSPI_TASK_READ_CRC_BYTES,

    /* Check if read operation is complete. */
    DRV_SDSPI_TASK_READ_COMPLETE_CHECK,

    /* Send Stop tran command to terminate a multi block read operation. */
    DRV_SDSPI_TASK_READ_STOP_TRANSMISSION,

    /* Send 8 clock pulses */
    DRV_SDSPI_TASK_SEND_DUMMY_CLOCK_PULSES,

    /* Send write start token to the SD card. */
    DRV_SDSPI_TASK_WRITE_START_TOKEN,

    /* Write 512 bytes of data to the SD card. */
    DRV_SDSPI_TASK_WRITE_DATA,

    /* Write 2 bytes of CRC data for the write block. */
    DRV_SDSPI_TASK_WRITE_CRC_BYTES,

    /* Wait for the response token from the card. */
    DRV_SDSPI_TASK_WRITE_READ_RESP_TOKEN,

    /* Check if the response token received is correct. */
    DRV_SDSPI_TASK_WRITE_RESP_TOKEN_STATUS,

    /* Read the busy status from the card. */
    DRV_SDSPI_TASK_WR_CHK_BSY,

    /* Check if the card is still busy with programming of the data. */
    DRV_SDSPI_TASK_WR_CHK_BSY_STAT,

    /* Check if the write is complete. */
    DRV_SDSPI_TASK_WRITE_COMPLETE_CHECK,

    /* Send the stop transmission token for multi block writes. */
    DRV_SDSPI_TASK_WRITE_STOP_TRAN_TOKEN,

    /* Send 8 clock pulses post stop tran token. */
    DRV_SDSPI_TASK_WR_STP_TRN_DUMMY_PLS,

    /* Read the card busy status. */
    DRV_SDSPI_TASK_WR_STP_TRAN_CHK_BSY,

    /* Check if the card has come out of the busy status. */
    DRV_SDSPI_TASK_WR_STP_TRAN_BSY_STAT,

    /* SD card write is complete */
    DRV_SDSPI_TASK_PROCESS_NEXT,

    /* Something went wrong on read/write */
    DRV_SDSPI_TASK_READ_WRITE_ABORT

} DRV_SDSPI_BUFFER_IO_TASK_STATES;

typedef enum
{
    /* SD Card is attached from the system */
    DRV_SDSPI_IS_DETACHED,

    /* SD Card is attached to the system */
    DRV_SDSPI_IS_ATTACHED

}DRV_SDSPI_ATTACH;

typedef enum
{
    /* Command code to reset the SD card */
    CMD_VALUE_GO_IDLE_STATE = 0,

    /* Command code to initialize the SD card */
    CMD_VALUE_SEND_OP_COND  = 1,

    /* This macro defined the command code to check for sector addressing */
    CMD_VALUE_SEND_IF_COND  = 8,

    /* Command code to get the Card Specific Data */
    CMD_VALUE_SEND_CSD      = 9,

    /* Command code to get the Card Information */
    CMD_VALUE_SEND_CID      = 10,

    /* Command code to stop transmission during a multi-block read */
    CMD_VALUE_STOP_TRANSMISSION = 12,

    /* Command code to get the card status information */
    CMD_VALUE_SEND_STATUS       = 13,

    /* Command code to set the block length of the card */
    CMD_VALUE_SET_BLOCKLEN      = 16,

    /* Command code to read one block from the card */
    CMD_VALUE_READ_SINGLE_BLOCK  = 17,

    /* Command code to read multiple blocks from the card */
    CMD_VALUE_READ_MULTI_BLOCK   = 18,

    /* Command code to tell the media how many blocks to pre-erase
     (for faster multi-block writes to follow)
     Note: This is an "application specific" command.  This tells the media how
     many blocks to pre-erase for the subsequent WRITE_MULTI_BLOCK */
    CMD_VALUE_SET_WR_BLK_ERASE_COUNT =  23,

    /* Command code to write one block to the card */
    CMD_VALUE_WRITE_SINGLE_BLOCK  = 24,

    /* Command code to write multiple blocks to the card */
    CMD_VALUE_WRITE_MULTI_BLOCK   = 25,

    /* Command code to set the address of the start of an erase operation */
    CMD_VALUE_TAG_SECTOR_START    = 32,

    /* Command code to set the address of the end of an erase operation */
    CMD_VALUE_TAG_SECTOR_END      = 33,

    /* Command code to erase all previously selected blocks */
    CMD_VALUE_ERASE              =  38,

    /* Command code to initialise an SD card and provide the CSD register value.
    Note: this is an "application specific" command (specific to SD cards)
    and must be preceded by CMD_APP_CMD */
    CMD_VALUE_SD_SEND_OP_COND     = 41,

    /* Command code to begin application specific command inputs */
    CMD_VALUE_APP_CMD             = 55,

    /* Command code to get the OCR register information from the card */
    CMD_VALUE_READ_OCR            = 58,

    /* Command code to disable CRC checking */
    CMD_VALUE_CRC_ON_OFF          = 59,

}DRV_SDSPI_COMMAND_VALUE;

typedef enum
{
    /* R1 type response */
    RESPONSE_R1,

    /* R1b type response */
    RESPONSE_R1b,

    /* R2 type response */
    RESPONSE_R2,

    /* R3 type response */
    RESPONSE_R3,

    /* R7 type response */
    RESPONSE_R7

}DRV_SDSPI_RESPONSES;

typedef enum
{
    /* Index of in the CMD_GO_IDLE_STATE command 'Command array' */
    DRV_SDSPI_GO_IDLE_STATE,

    /* Index of in the CMD_SEND_OP_COND command 'Command array' */
    DRV_SDSPI_SEND_OP_COND,

    /* Index of in the CMD_SEND_IF_COND command 'Command array' */
    DRV_SDSPI_SEND_IF_COND,

    /* Index of in the CMD_SEND_CSD command 'Command array' */
    DRV_SDSPI_SEND_CSD,

    /* Index of in the CMD_SEND_CID command 'Command array' */
    DRV_SDSPI_SEND_CID,

    /* Index of in the CMD_STOP_TRANSMISSION command 'Command array' */
    DRV_SDSPI_STOP_TRANSMISSION,

    /* Index of in the CMD_SEND_STATUS command 'Command array' */
    DRV_SDSPI_SEND_STATUS,

    /* Index of in the CMD_SET_BLOCKLEN command 'Command array' */
    DRV_SDSPI_SET_BLOCKLEN,

    /* Index of in the CMD_READ_SINGLE_BLOCK command 'Command array' */
    DRV_SDSPI_READ_SINGLE_BLOCK,

    /* Index of in the CMD_READ_MULTI_BLOCK command 'Command array' */
    DRV_SDSPI_READ_MULTI_BLOCK,

    /* Index of in the CMD_WRITE_SINGLE_BLOCK command 'Command array' */
    DRV_SDSPI_WRITE_SINGLE_BLOCK,

    /* Index of in the CMD_WRITE_MULTI_BLOCK command 'Command array' */
    DRV_SDSPI_WRITE_MULTI_BLOCK,

    /* Index of in the CMD_TAG_SECTOR_START command 'Command array' */
    DRV_SDSPI_TAG_SECTOR_START,

    /* Index of in the CMD_TAG_SECTOR_END command 'Command array' */
    DRV_SDSPI_TAG_SECTOR_END,

    /* Index of in the CMD_ERASE command 'Command array' */
    DRV_SDSPI_ERASE,

    /* Index of in the CMD_APP_CMD command 'Command array' */
    DRV_SDSPI_APP_CMD,

    /* Index of in the CMD_READ_OCR command 'Command array' */
    DRV_SDSPI_READ_OCR,

    /* Index of in the CMD_CRC_ON_OFF command 'Command array' */
    DRV_SDSPI_CRC_ON_OFF,

    /* Index of in the CMD_SD_SEND_OP_COND command 'Command array' */
    DRV_SDSPI_SD_SEND_OP_COND,

    /* Index of in the CMD_SET_WR_BLK_ERASE_COUNT command 'Command array' */
    DRV_SDSPI_SET_WR_BLK_ERASE_COUNT

}DRV_SDSPI_COMMANDS;

typedef enum
{
    /* Normal SD Card */
    DRV_SDSPI_MODE_NORMAL,

    /* SDHC type Card */
    DRV_SDSPI_MODE_HC

}DRV_SDSPI_TYPE;

/* MISRA C-2023 Rule 5.2 deviated:2 Deviation record ID -  H3_MISRAC_2023_R_5_2_DR_1 */

typedef enum
{
    /* Initial state */
    DRV_SDSPI_CMD_DETECT_START_INIT,

    /* Check for the presence of the SD card */
    DRV_SDSPI_CMD_DETECT_CHK_FOR_CARD,

    /* Reset the SD card */
    DRV_SDSPI_CMD_DETECT_RESET_SDCARD,

    /* Placeholder state until the MediaInitialize function indicates if the card
    is really present or not. */
    DRV_SDSPI_CMD_DETECT_WAIT_TRANSFER_COMPLETE,

    /* Check whether the card has been detached. */
    DRV_SDSPI_CMD_DETECT_CHK_FOR_DETCH,

    DRV_SDSPI_CMD_DETECT_CHK_FOR_CMD_SEND,

    DRV_SDSPI_CMD_DETECT_CHK_FR_DETACH_RD_CID_DAT,

    DRV_SDSPI_CMD_DETECT_CHK_FOR_DETACH_PRCS_CID_DAT,

    DRV_SDSPI_CMD_DETECT_IDLE_STATE,

} DRV_SDSPI_CMD_DETECT_STATES;

/* MISRAC 2012 deviation block end */

typedef enum
{
    /* Frame the command packet and drive the CS low. */
    DRV_SDSPI_CMD_FRAME_PACKET,

    /* Send the framed command packet. */
    DRV_SDSPI_CMD_SEND_PACKET,
    /* DRV_SDSPI_STOP_TRANSMISSION command is a special case
       that requires an additional read. */
    DRV_SDSPI_CMD_CHECK_SPL_CASE,

    /* Check whether the command processing is complete */
    DRV_SDSPI_CMD_CHECK_TRANSFER_COMPLETE,

    /* Act as per the expected response type for the command */
    DRV_SDSPI_CMD_CHECK_RESP_TYPE,

    /* Switch to this when the response type is R2 */
    DRV_SDSPI_CMD_HANDLE_R2_RESPONSE,

    /* Switch to this when the response type is R7 */
    DRV_SDSPI_CMD_HANDLE_R7_RESPONSE,

    /* Read back the data until the card is not busy */
    DRV_SDSPI_CMD_R1B_READ_BACK,

    /* Check for command execution completion */
    DRV_SDSPI_CMD_EXEC_CHECK_COMPLETION,

    /* Temporary state */
    DRV_SDSPI_CMD_CONFIRM_COMPLETE,

    DRV_SDSPI_CMD_CONFIRM_EXEC_ERROR,

    /* Error state */
    DRV_SDSPI_CMD_EXEC_ERROR,

    /* Command execution is complete */
    DRV_SDSPI_CMD_EXEC_IS_COMPLETE,

}DRV_SDSPI_CMD_STATES;

typedef enum
{
    /* Keep the CS high */
    DRV_SDSPI_INIT_CHIP_DESELECT,

    /* Card ramp up time. Issue clock cycles. */
    DRV_SDSPI_INIT_RAMP_TIME,

    /* Check if the card is ramped up */
    DRV_SDSPI_INIT_RAMP_TIME_STATUS,

    /* Enable the CS */
    DRV_SDSPI_INIT_CHIP_SELECT,

    /* Reset the SD Card using CMD0 */
    DRV_SDSPI_INIT_RESET_SDCARD,

    /* Check the card's interface condition */
    DRV_SDSPI_INIT_CHK_IFACE_CONDITION,

    /* Send OCR to expand the ACMD41 */
    DRV_SDSPI_INIT_READ_OCR_REGISTER,

    /* Send APP CMD */
    DRV_SDSPI_INIT_SEND_APP_CMD,

    /* Send APP CMD ACMD41 to check if the card's internal init is done */
    DRV_SDSPI_INIT_SEND_ACMD41,

    /* Read the Card's Operating Conditions Register */
    DRV_SDSPI_INIT_READ_OCR,

    /* Card's internal init is complete. Increase the SPI frequency. */
    DRV_SDSPI_INIT_INCR_CLK_SPD,

    /* Wait for the dummy read done in the INCR_CLOCK_SPEED state to complete. */
    DRV_SDSPI_INIT_INCR_CLK_SPD_STAT,

    /* Issue command to read the card's Card Specific Data register */
    DRV_SDSPI_INIT_READ_CSD,

    /* Read the CSD data */
    DRV_SDSPI_INIT_READ_CSD_DATA,

    /* Read the CSD data token */
    DRV_SDSPI_INIT_RD_CSD_DAT_TKN,

    /* Read the CSD data token */
    DRV_SDSPI_INIT_RD_CSD_DAT_TKN_STAT,

    /* Process the CSD register data */
    DRV_SDSPI_INIT_PROCESS_CSD,

    /* Issue command to read the card's Card Identification Data register */
    DRV_SDSPI_INIT_READ_CID,

    /* Read the CID data */
    DRV_SDSPI_INIT_READ_CID_DATA,

    /* Process the CID register data */
    DRV_SDSPI_INIT_PROCESS_CID,

    /* Issue command to turn off the CRC */
    DRV_SDSPI_INIT_TURN_OFF_CRC,

    /* Set the block length of the card */
    DRV_SDSPI_INIT_SET_BLOCKLEN,

    /* SD Card Init is done */
    DRV_SDSPI_INIT_SD_INIT_DONE,

    /* Error initializing the SD card */
    DRV_SDSPI_INIT_ERROR

} DRV_SDSPI_INIT_STATE;

typedef struct
{
    /* Command code */
    DRV_SDSPI_COMMAND_VALUE      commandCode;

    /* CRC value for that command */
    uint8_t                     crc;

    /* Response type */
    DRV_SDSPI_RESPONSES         responseType;

    /* Response Length */
    uint32_t                    responseLength;

} DRV_SDSPI_CMD_OBJ;

/* MISRA C-2023 Rule 6.1 deviated:5 Deviation record ID -  H3_MISRAC_2023_R_6_1_DR_1 */

typedef union
{
    /* This structure allows array-style access of command bytes */
    struct
    {
        uint8_t field[7];
    };

    /* This structure allows byte-wise access of packet command bytes */
    struct
    {
        /* The CRC byte */
        uint8_t crc;

        /* Filler space (since bitwise declarations can't
         cross a uint32_t boundary) */
        uint8_t c32filler[3];

        /* Address byte 0 */
        uint8_t address0;

        /* Address byte 1 */
        uint8_t address1;

        /* Address byte 2 */
        uint8_t address2;

        /* Address byte 3 */
        uint8_t address3;

        /* Command code byte */
        uint8_t cmd;
    };

    /* This structure allows bitwise access to elements of the command bytes */
    struct
    {
        /* Packet end bit */
        uint8_t  endBit:1;

        /* CRC value */
        uint8_t  crc7:7;

        /* Address */
        uint32_t    address;

        /* Command code */
        uint8_t  cmdIndex:6;

        /* Transmit bit */
        uint8_t  transmitBit:1;

        /* Packet start bit */
        uint8_t  startBit:1;
    };
} DRV_SDSPI_CMD_PACKET;

/* MISRAC 2012 deviation block end */

typedef union
{
    /* Byte-wise access */
    uint8_t byte;

    /* This structure allows bitwise access of the response */
    struct
    {
        /* Card is in idle state */
        unsigned inIdleState:1;

        /* Erase reset flag */
        unsigned eraseReset:1;

        /* Illegal command flag */
        unsigned illegalCommand:1;

        /* CRC error flag */
        unsigned crcError:1;

        /* Erase sequence error flag */
        unsigned eraseSequenceError:1;

        /* Address error flag */
        unsigned addressError:1;

        /* Parameter flag */
        unsigned parameterError:1;

        /* Unused bit 7 */
        unsigned unusedB7:1;
    }task;

} DRV_SDSPI_RESPONSE_1;

typedef union
{
    /* Get both the bytes */
    uint16_t word;

    struct
    {
        /* Byte-wise access */
        uint8_t      byte0;
        uint8_t      byte1;
    }bytes;
    struct
    {
        /* Card is in idle state */
        unsigned inIdleState:1;

        /* Erase reset flag */
        unsigned eraseReset:1;

        /* Illegal command flag */
        unsigned illegalCommand:1;

        /* CRC error flag */
        unsigned crcError:1;

        /* Erase sequence error flag */
        unsigned eraseSequenceError:1;

        /* Address error flag */
        unsigned addressError:1;

        /* Parameter error flag */
        unsigned parameterError:1;

        /* Un-used bit */
        unsigned unusedB7:1;

        /* Card is locked? */
        unsigned cardIsLocked:1;

        /* WP erase skip| lock/unlock command failed */
        unsigned wpEraseSkipLockFail:1;

        /* Error */
        unsigned error:1;

        /* CC error */
        unsigned ccError:1;

        /* Card ECC fail */
        unsigned cardEccFail:1;

        /* WP violation */
        unsigned wpViolation:1;

        /* Erase parameter */
        unsigned eraseParam:1;

        /* out of range or CSD over write */
        unsigned outrangeCsdOverWrite:1;
    }task;

} DRV_SDSPI_RESPONSE_2;
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
